jasonsbeer/Amiga-N2630/DataSheet/TimingDiagrams/6800-6502 STATE MACHINE READ.png

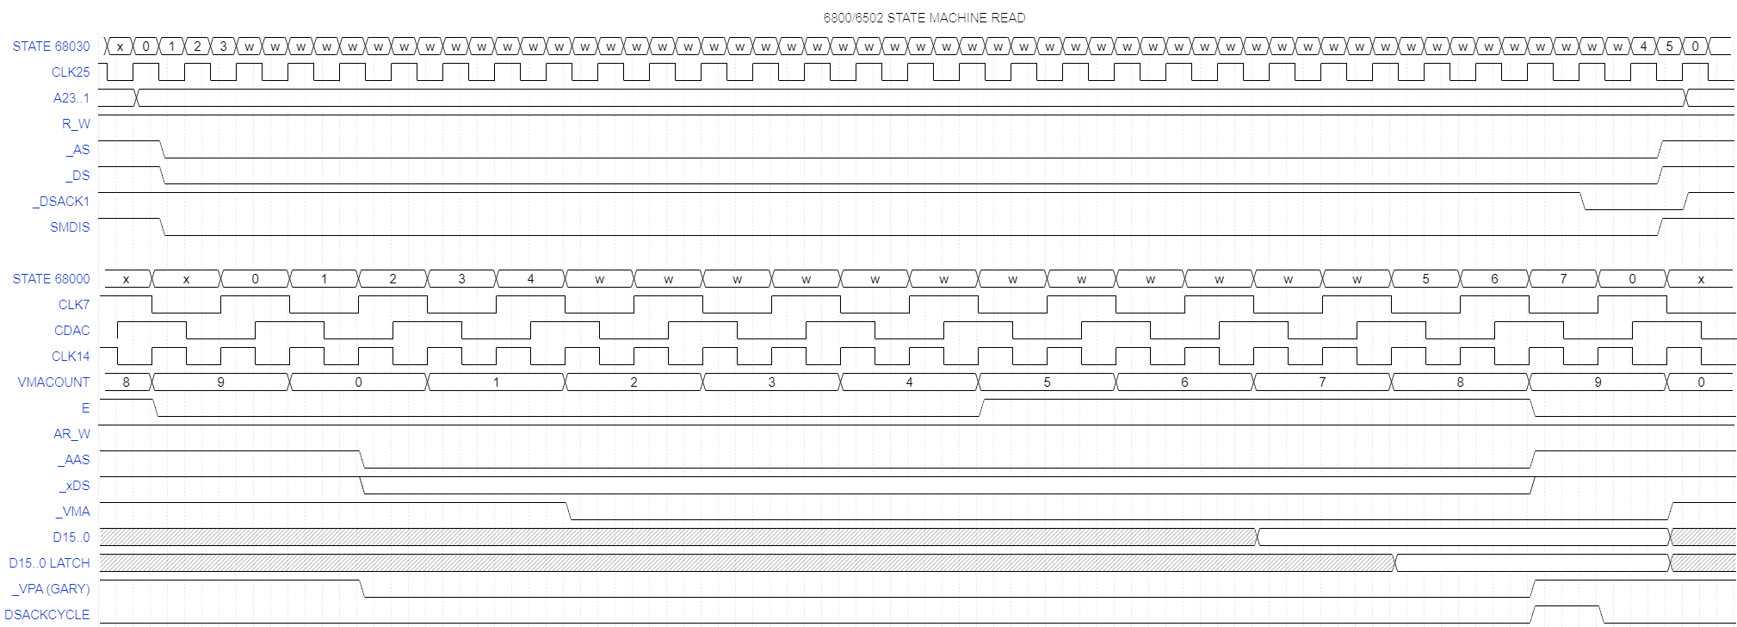
DataSheet/TimingDiagrams/6800-6502 STATE MACHINE READ.png
