jasonsbeer/Amiga-N2630/DataSheet/TimingDiagrams/68000 STATE MACHINE READ.png

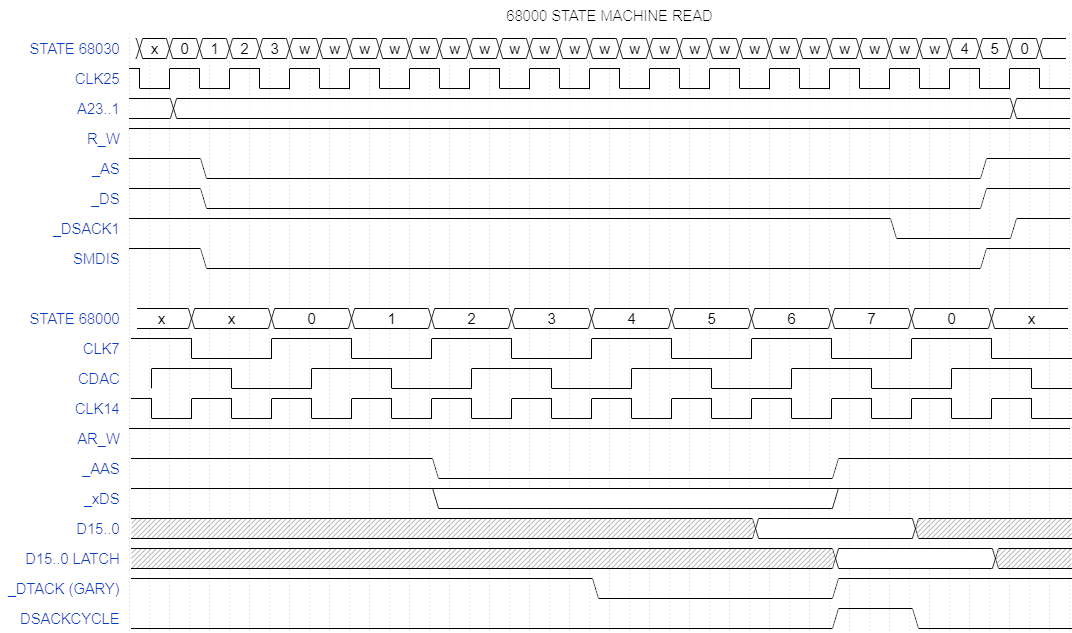
DataSheet/TimingDiagrams/68000 STATE MACHINE READ.png
