jasonsbeer/Amiga-N2630/DataSheet/TimingDiagrams/68000 STATE MACHINE WRITE.png

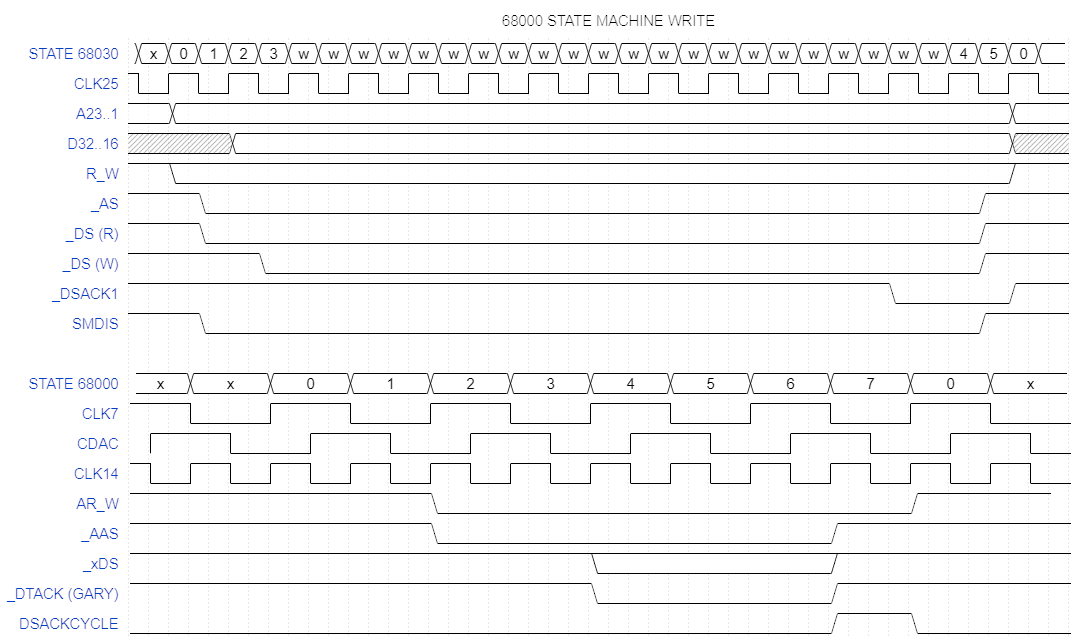
DataSheet/TimingDiagrams/68000 STATE MACHINE WRITE.png
