jasonsbeer/Amiga-N2630/DataSheet/TimingDiagrams/DMA STATE MACHINE READ.png

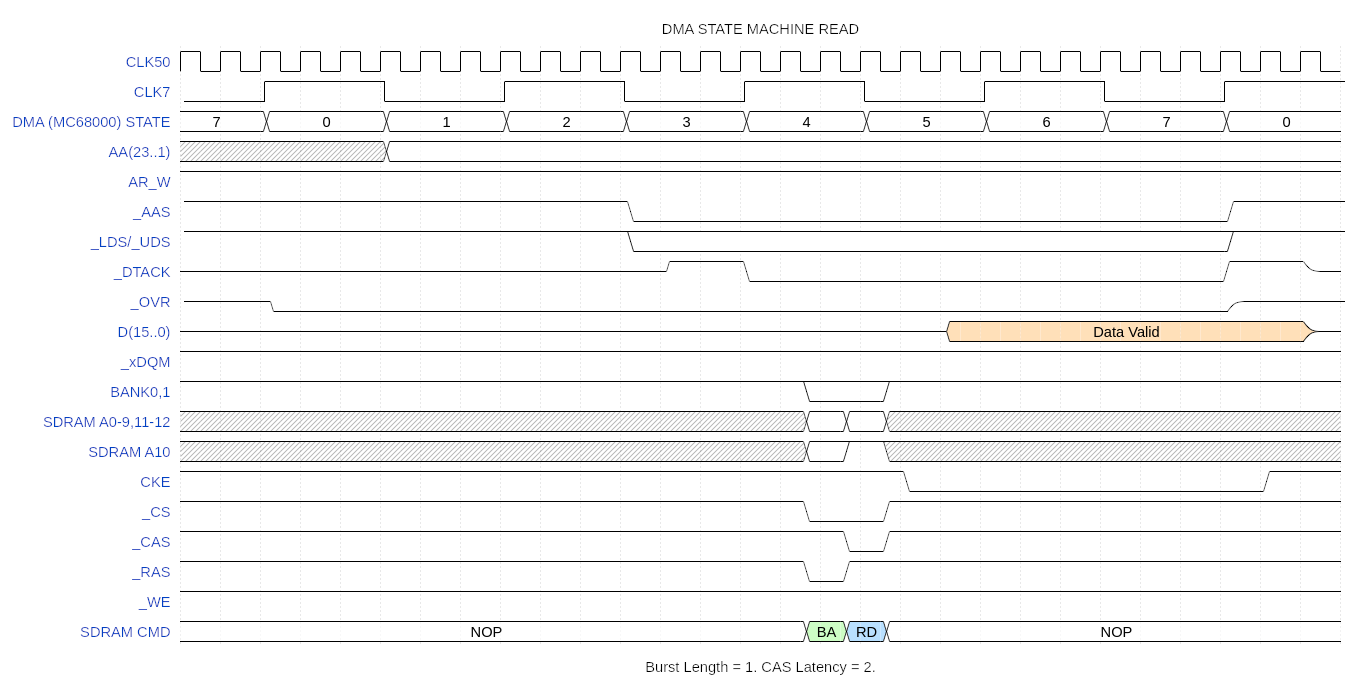
DataSheet/TimingDiagrams/DMA STATE MACHINE READ.png
