jasonsbeer/Amiga-N2630/DataSheet/TimingDiagrams/DMA STATE MACHINE WRITE.png

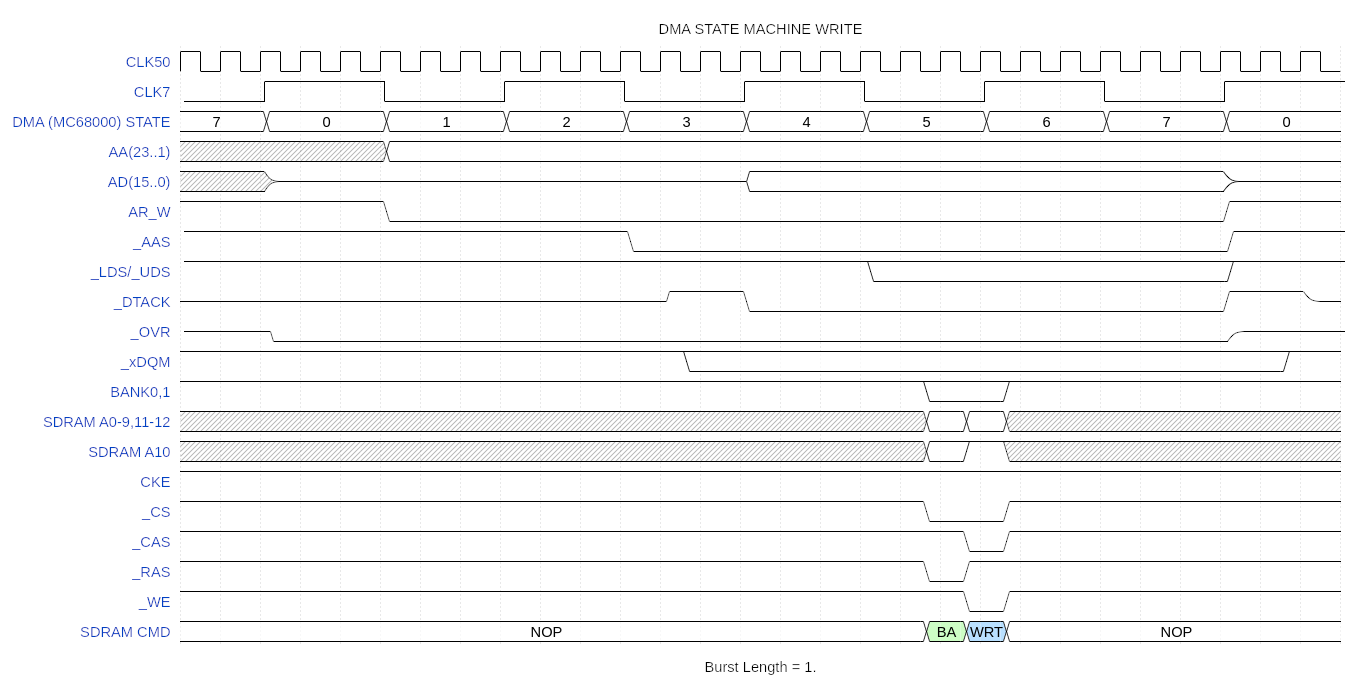
DataSheet/TimingDiagrams/DMA STATE MACHINE WRITE.png
