jasonsbeer/Amiga-N2630/DataSheet/TimingDiagrams/ZORRO2-SDRAM.png

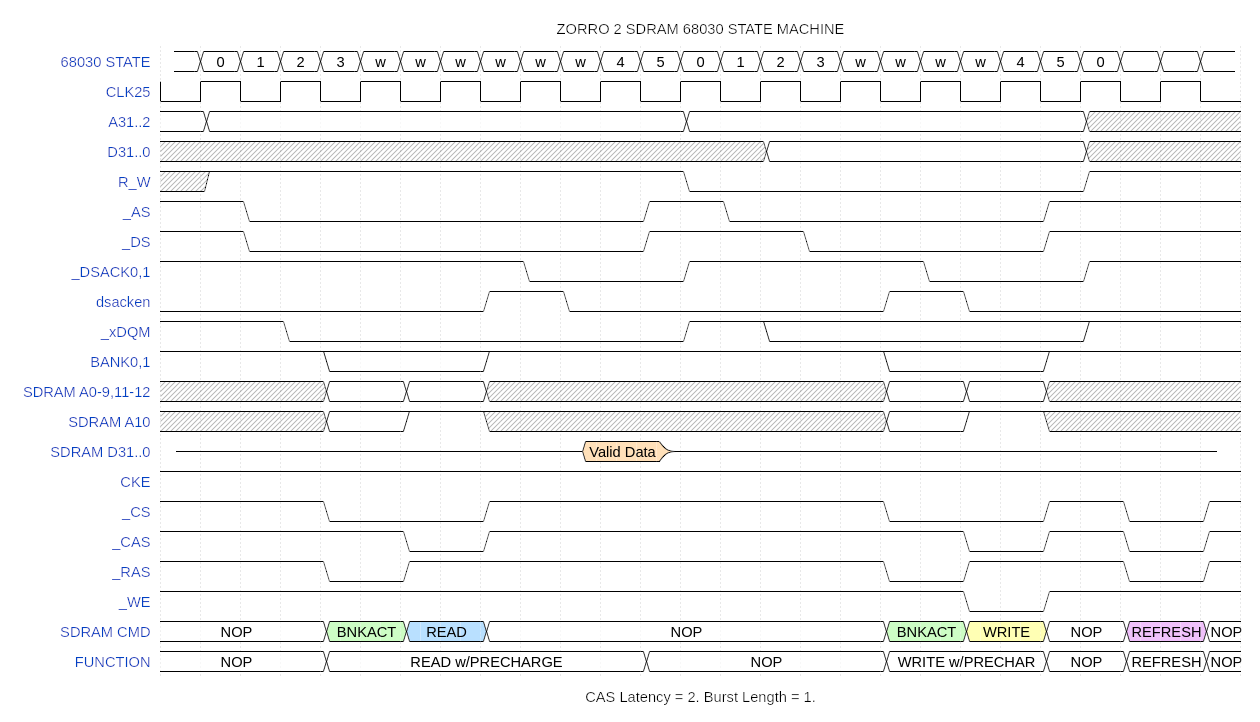
DataSheet/TimingDiagrams/ZORRO2-SDRAM.png
