jasonsbeer/Amiga-N2630/DataSheet/TimingDiagrams/ZORRO3-SDRAM.png

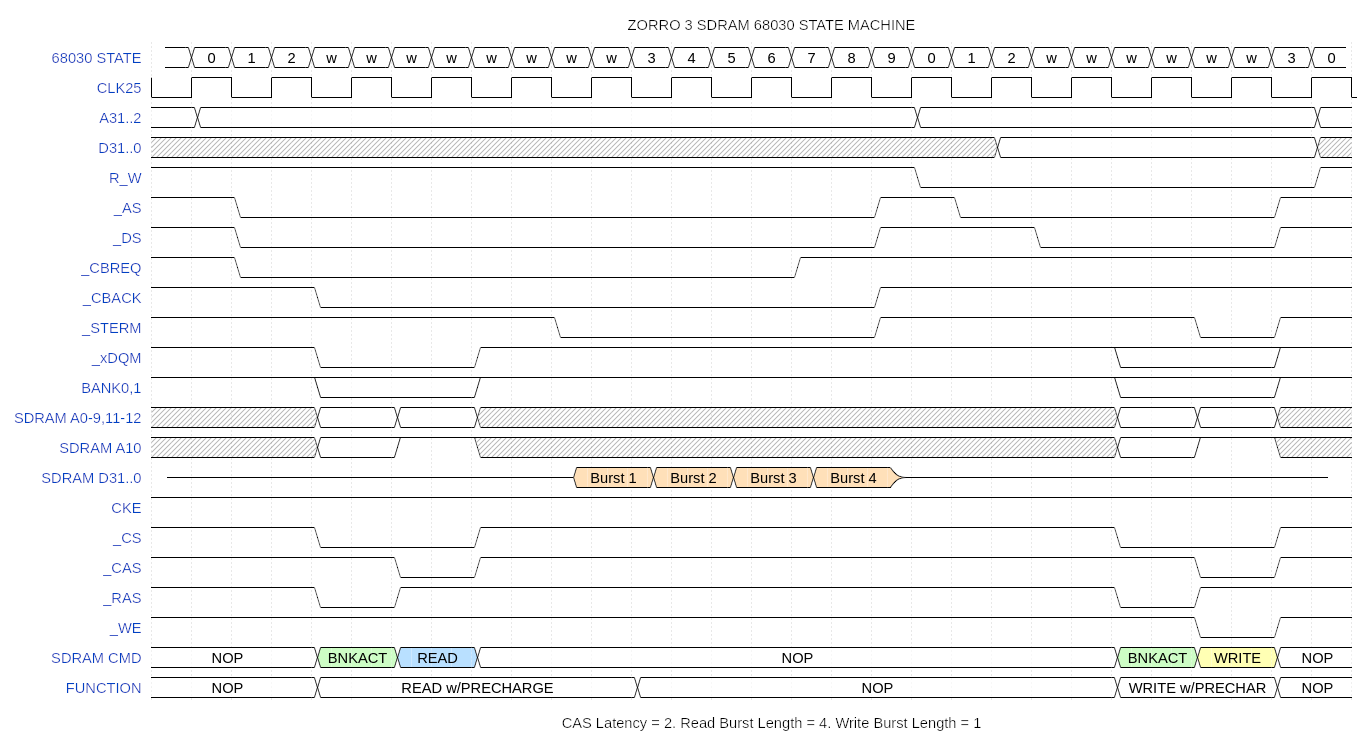
DataSheet/TimingDiagrams/ZORRO3-SDRAM.png
