jasonsbeer/Amiga-N2630/Images/N2630-30-small.jpg

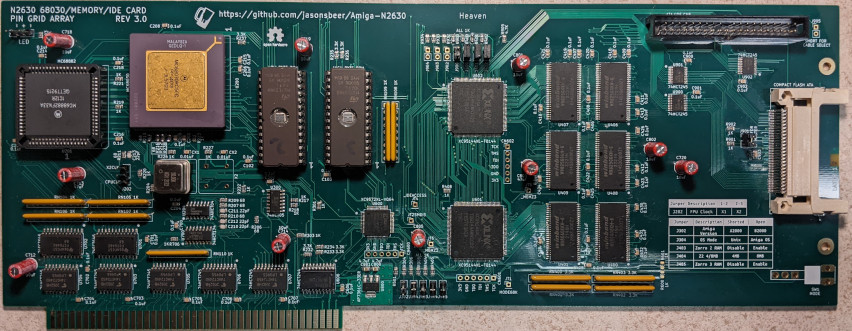
Images/N2630-30-small.jpg
