jasonsbeer/Amiga-N2630/Images/N2630-30D.png

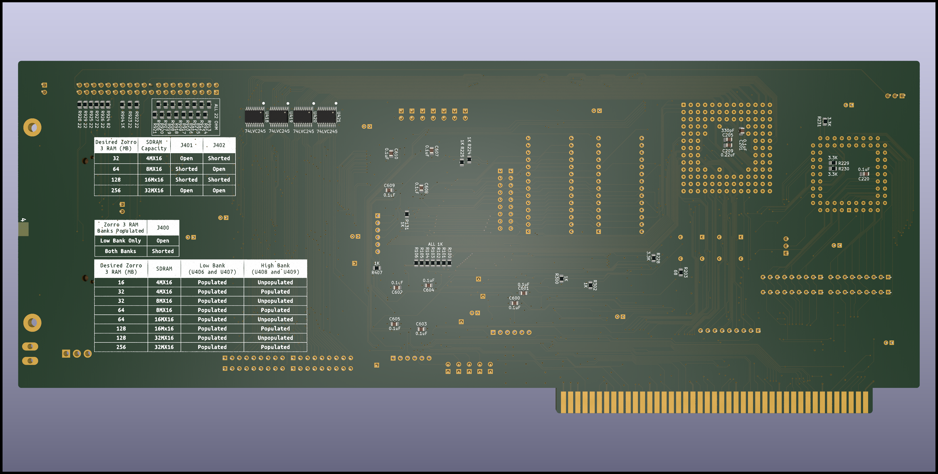
Images/N2630-30D.png
