jasonsbeer/Amiga-N2630/KiCAD/A2630-New-KiCAD-Rev410-PGA/BaseMemory.kicad_sch

## KiCad design KiCAD/A2630-New-KiCAD-Rev410-PGA/BaseMemory.kicad_sch (2024-03-27)

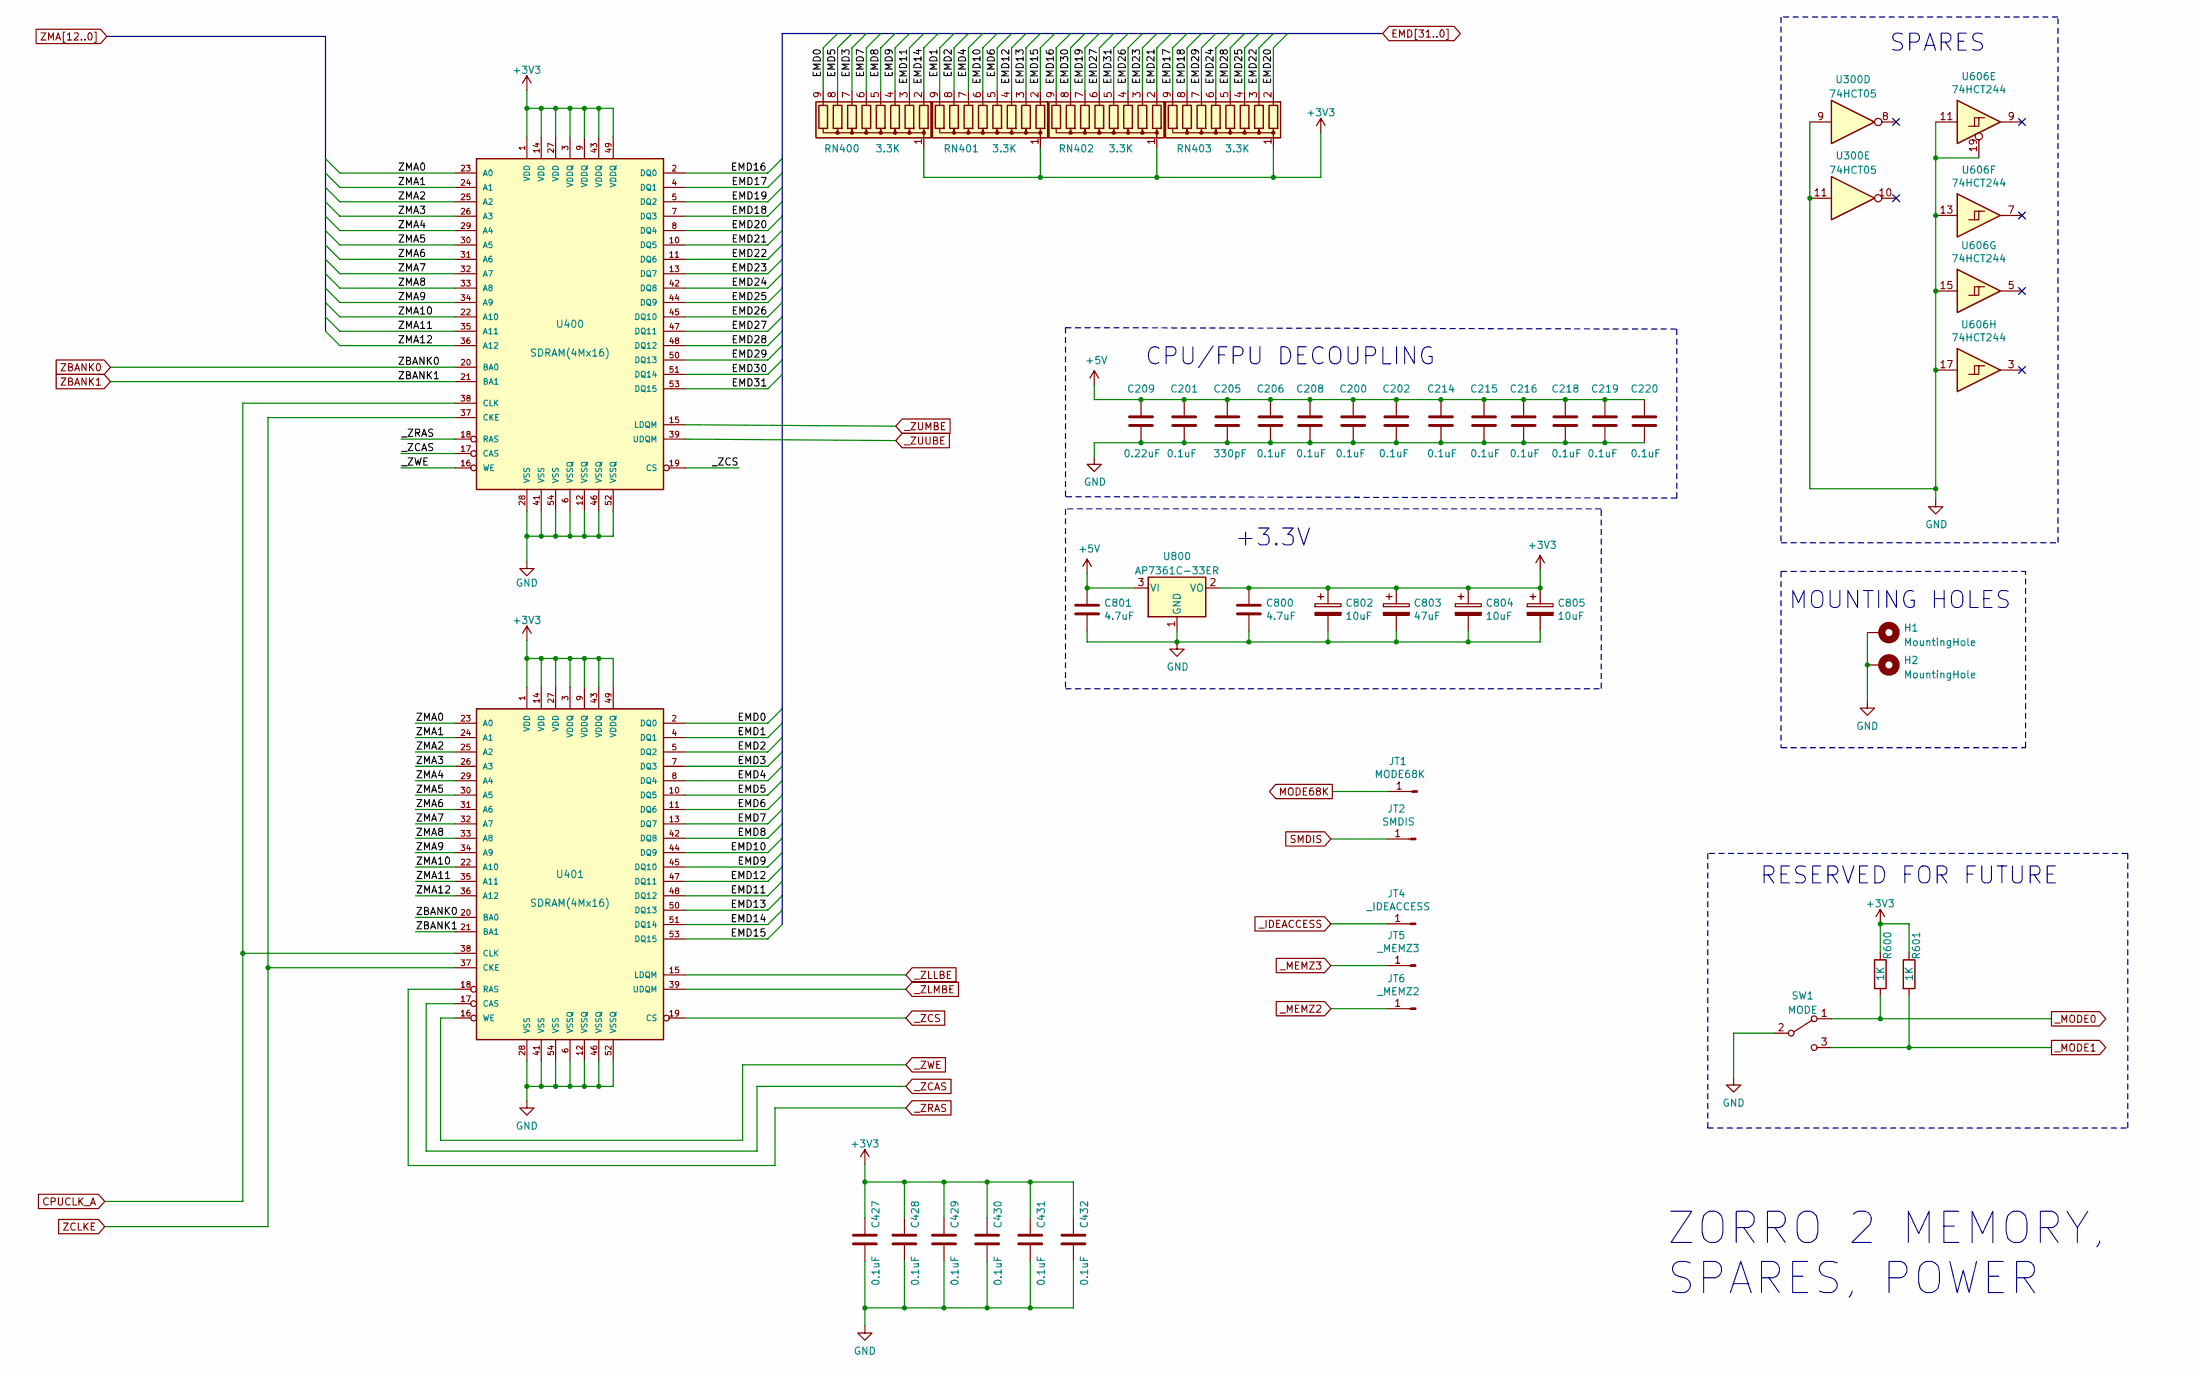
[picture p69: schematic BaseMemory.kicad_sch]

Parts:
C200, C201, C202, C206, C208, C214, C215, C216, C218, C219, C220, C427, C428, C429, C430, C431, C432: 0.1uF; C_0805_2012Metric
C205: 330pF; C_0805_2012Metric
C209: 0.22uF; C_0805_2012Metric
C800, C801: 4.7uF; C_0805_2012Metric
C802, C804, C805: 10uF; CP_Radial_D5.0mm_P2.00mm
C803: 47uF; CP_Radial_D5.0mm_P2.00mm
H1, H2: MountingHole; MountingHole_3.2mm_M3_Pad
JT1: MODE68K; PinHeader_1x01_P2.54mm_Vertical
JT2: SMDIS; PinHeader_1x01_P2.54mm_Vertical
JT4: _IDEACCESS; PinHeader_1x01_P2.54mm_Vertical
JT5: _MEMZ3; PinHeader_1x01_P2.54mm_Vertical
JT6: _MEMZ2; PinHeader_1x01_P2.54mm_Vertical
R600, R601: 1K; R_0805_2012Metric
RN400, RN401, RN402, RN403: 3.3K; R_Array_SIP9
SW1: MODE; 100SP1T1B1M7QE; PART 100SP1T1B1M7QE
U300: 74HCT05; SOIC-14_3.9x8.7mm_P1.27mm
U400, U401: SDRAM(4Mx16); TSOP-II-54_22.2x10.16mm_P0.8mm
U606: 74HCT244; SOIC-20W_7.5x12.8mm_P1.27mm
U800: AP7361C-33ER; SOT-223-3_TabPin2

Connections:
+3V3: C427.1, C428.1, C429.1, C430.1, C431.1, C432.1, C800.1, C802.1, C803.1, C804.1, C805.1, R600.1, R601.1, RN400.1 (common), RN401.1 (common), RN402.1 (common), RN403.1 (common), U400.1 (VDD), U400.3 (VDDQ), U400.9 (VDDQ), U400.14 (VDD), U400.27 (VDD), U400.43 (VDDQ), U400.49 (VDDQ), U401.1 (VDD), U401.3 (VDDQ), U401.9 (VDDQ), U401.14 (VDD), U401.27 (VDD), U401.43 (VDDQ), U401.49 (VDDQ), U800.2 (VO)
+5V: C200.1, C201.1, C202.1, C205.1, C206.1, C208.1, C209.1, C214.1, C215.1, C216.1, C218.1, C219.1, C220.1, C801.1, U800.3 (VI)
CPUCLK_A: U400.38 (CLK), U401.38 (CLK)
EMD0: RN400.9 (R8), U401.2 (DQ0)
EMD1: RN401.9 (R8), U401.4 (DQ1)
EMD2: RN401.8 (R7), U401.5 (DQ2)
EMD3: RN400.7 (R6), U401.7 (DQ3)
EMD4: RN401.7 (R6), U401.8 (DQ4)
EMD5: RN400.8 (R7), U401.10 (DQ5)
EMD6: RN401.5 (R4), U401.11 (DQ6)
EMD7: RN400.6 (R5), U401.13 (DQ7)
EMD8: RN400.5 (R4), U401.42 (DQ8)
EMD9: RN400.4 (R3), U401.45 (DQ10)
EMD10: RN401.6 (R5), U401.44 (DQ9)
EMD11: RN400.3 (R2), U401.48 (DQ12)
EMD12: RN401.4 (R3), U401.47 (DQ11)
EMD13: RN401.3 (R2), U401.50 (DQ13)
EMD14: RN400.2 (R1), U401.51 (DQ14)
EMD15: RN401.2 (R1), U401.53 (DQ15)
EMD16: RN402.9 (R8), U400.2 (DQ0)
EMD17: RN403.9 (R8), U400.4 (DQ1)
EMD18: RN403.8 (R7), U400.7 (DQ3)
EMD19: RN402.7 (R6), U400.5 (DQ2)
EMD20: RN403.2 (R1), U400.8 (DQ4)
EMD21: RN402.2 (R1), U400.10 (DQ5)
EMD22: RN403.3 (R2), U400.11 (DQ6)
EMD23: RN402.3 (R2), U400.13 (DQ7)
EMD24: RN403.6 (R5), U400.42 (DQ8)
EMD25: RN403.4 (R3), U400.44 (DQ9)
EMD26: RN402.4 (R3), U400.45 (DQ10)
EMD27: RN402.6 (R5), U400.47 (DQ11)
EMD28: RN403.5 (R4), U400.48 (DQ12)
EMD29: RN403.7 (R6), U400.50 (DQ13)
EMD30: RN402.8 (R7), U400.51 (DQ14)
EMD31: RN402.5 (R4), U400.53 (DQ15)
GND: C200.2, C201.2, C202.2, C205.2, C206.2, C208.2, C209.2, C214.2, C215.2, C216.2, C218.2, C219.2, C220.2, C427.2, C428.2, C429.2, C430.2, C431.2, C432.2, C800.2, C801.2, C802.2, C803.2, C804.2, C805.2, H1.1, H2.1, SW1.2 (B), U300.9, U300.11, U400.6 (VSSQ), U400.12 (VSSQ), U400.28 (VSS), U400.41 (VSS), U400.46 (VSSQ), U400.52 (VSSQ), U400.54 (VSS), U401.6 (VSSQ), U401.12 (VSSQ), U401.28 (VSS), U401.41 (VSS), U401.46 (VSSQ), U401.52 (VSSQ), U401.54 (VSS), U606.11, U606.13, U606.15, U606.17, U606.19, U800.1 (GND)
MODE68K: JT1.1
SMDIS: JT2.1
ZBANK0: U400.20 (BA0), U401.20 (BA0)
ZBANK1: U400.21 (BA1), U401.21 (BA1)
ZCLKE: U400.37 (CKE), U401.37 (CKE)
ZMA0: U400.23 (A0), U401.23 (A0)
ZMA1: U400.24 (A1), U401.24 (A1)
ZMA2: U400.25 (A2), U401.25 (A2)
ZMA3: U400.26 (A3), U401.26 (A3)
ZMA4: U400.29 (A4), U401.29 (A4)
ZMA5: U400.30 (A5), U401.30 (A5)
ZMA6: U400.31 (A6), U401.31 (A6)
ZMA7: U400.32 (A7), U401.32 (A7)
ZMA8: U400.33 (A8), U401.33 (A8)
ZMA9: U400.34 (A9), U401.34 (A9)
ZMA10: U400.22 (A10), U401.22 (A10)
ZMA11: U400.35 (A11), U401.35 (A11)
ZMA12: U400.36 (A12), U401.36 (A12)
_IDEACCESS: JT4.1
_MEMZ2: JT6.1
_MEMZ3: JT5.1
_MODE0: R600.2, SW1.1 (A)
_MODE1: R601.2, SW1.3 (C)
_ZCAS: U400.17 (CAS), U401.17 (CAS)
_ZCS: U400.19 (CS), U401.19 (CS)
_ZLLBE: U401.15 (LDQM)
_ZLMBE: U401.39 (UDQM)
_ZRAS: U400.18 (RAS), U401.18 (RAS)
_ZUMBE: U400.15 (LDQM)
_ZUUBE: U400.39 (UDQM)
_ZWE: U400.16 (WE), U401.16 (WE)

Notes on the sheet:
ZORRO 2 MEMORY, SPARES, POWER
MOUNTING HOLES
+3.3V
RESERVED FOR FUTURE
CPU/FPU DECOUPLING
SPARES
