jasonsbeer/Amiga-N2630/KiCAD/A2630-New-KiCAD-Rev410-PGA/CPLD1.kicad_sch

## KiCad design KiCAD/A2630-New-KiCAD-Rev410-PGA/CPLD1.kicad_sch (2024-03-27)

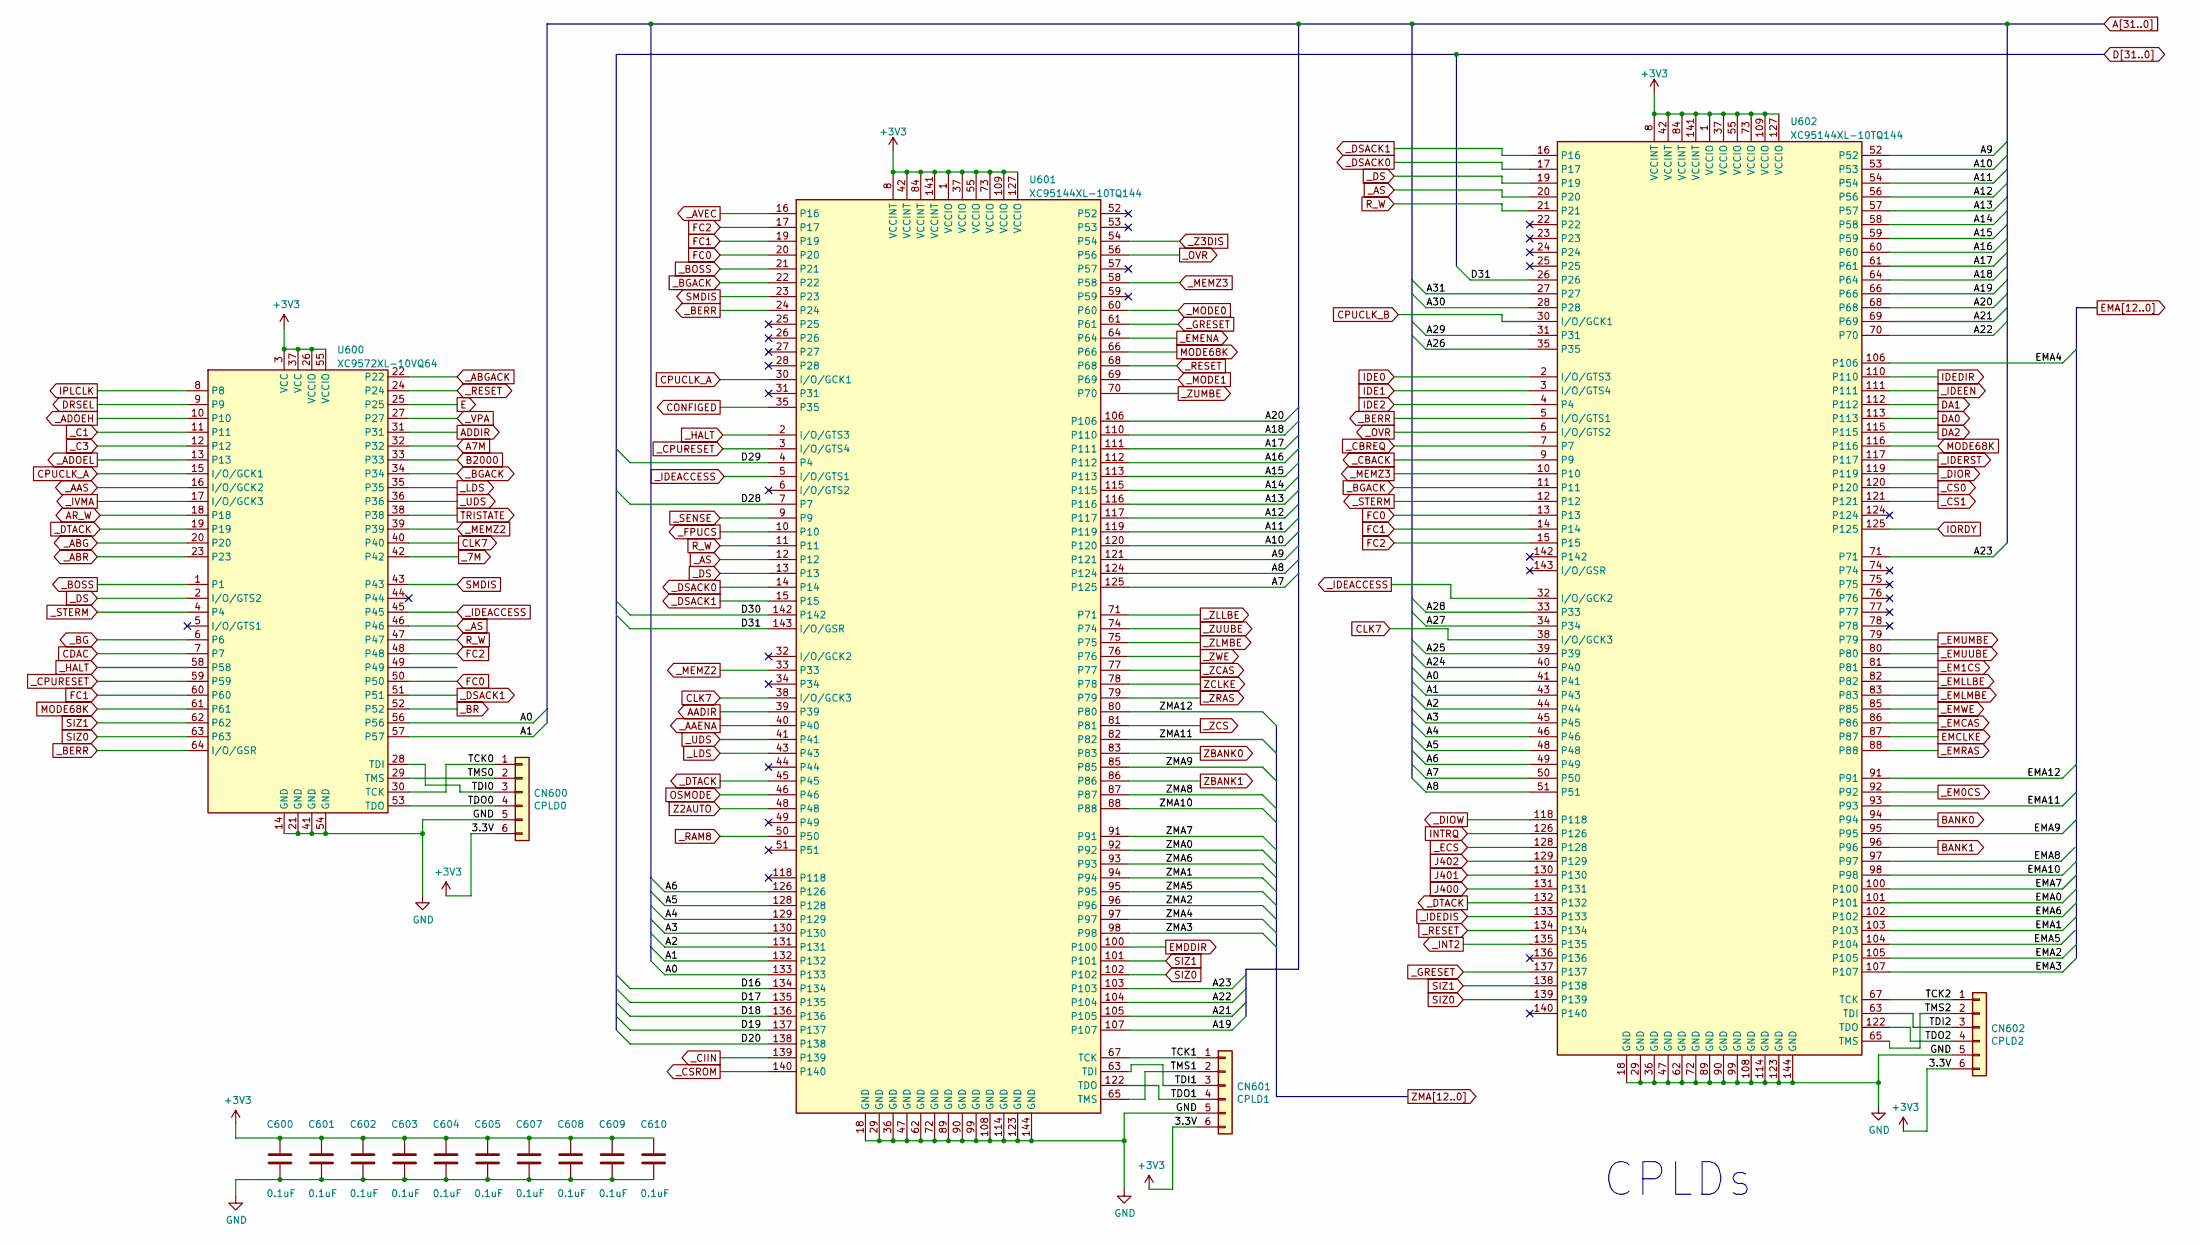
[picture p70: schematic CPLD1.kicad_sch]

Parts:
C600, C601, C602, C603, C604, C605, C607, C608, C609, C610: 0.1uF; C_0805_2012Metric
CN600: CPLD0; PinHeader_1x06_P2.54mm_Vertical
CN601: CPLD1; PinHeader_1x06_P2.54mm_Vertical
CN602: CPLD2; PinHeader_1x06_P2.54mm_Vertical
U600: XC9572XL-10VQ64; TQFP-64_10x10mm_P0.5mm
U601, U602: XC95144XL-10TQ144; TQFP-144_20x20mm_P0.5mm

Connections:
+3V3: C600.1, C601.1, C602.1, C603.1, C604.1, C605.1, C607.1, C608.1, C609.1, C610.1, CN600.6, CN601.6, CN602.6, U600.3 (VCC), U600.26 (VCCIO), U600.37 (VCC), U600.55 (VCCIO), U601.1 (VCCIO), U601.8 (VCCINT), U601.37 (VCCIO), U601.42 (VCCINT), U601.55 (VCCIO), U601.73 (VCCIO), U601.84 (VCCINT), U601.109 (VCCIO), U601.127 (VCCIO), U601.141 (VCCINT), U602.1 (VCCIO), U602.8 (VCCINT), U602.37 (VCCIO), U602.42 (VCCINT), U602.55 (VCCIO), U602.73 (VCCIO), U602.84 (VCCINT), U602.109 (VCCIO), U602.127 (VCCIO), U602.141 (VCCINT)
A0: U600.56, U601.133, U602.41
A1: U600.57, U601.132, U602.43
A2: U601.131, U602.44
A3: U601.130, U602.45
A4: U601.129, U602.46
A5: U601.128, U602.48
A6: U601.126, U602.49
A7: U601.125, U602.50
A7M: U600.32
A8: U601.124, U602.51
A9: U601.121, U602.52
A10: U601.120, U602.53
A11: U601.119, U602.54
A12: U601.117, U602.56
A13: U601.116, U602.57
A14: U601.115, U602.58
A15: U601.113, U602.59
A16: U601.112, U602.60
A17: U601.111, U602.61
A18: U601.110, U602.64
A19: U601.107, U602.66
A20: U601.106, U602.68
A21: U601.105, U602.69
A22: U601.104, U602.70
A23: U601.103, U602.71
A24: U602.40
A25: U602.39
A26: U602.35
A27: U602.34
A28: U602.33
A29: U602.31
A30: U602.28
A31: U602.27
AADIR: U601.39
ADDIR: U600.31
AR_W: U600.18
B2000: U600.33
BANK0: U602.94
BANK1: U602.96
CDAC: U600.7
CLK7: U600.40, U601.38 (I/O/GCK3), U602.38 (I/O/GCK3)
CONFIGED: U601.35
CPUCLK_A: U600.15 (I/O/GCK1), U601.30 (I/O/GCK1)
CPUCLK_B: U602.30 (I/O/GCK1)
D16: U601.134
D17: U601.135
D18: U601.136
D19: U601.137
D20: U601.138
D28: U601.7
D29: U601.4
D30: U601.142
D31: U601.143 (I/O/GSR), U602.26
DA0: U602.113
DA1: U602.112
DA2: U602.115
DRSEL: U600.9
E: U600.25
EMA0: U602.101
EMA1: U602.103
EMA2: U602.105
EMA3: U602.107
EMA4: U602.106
EMA5: U602.104
EMA6: U602.102
EMA7: U602.100
EMA8: U602.97
EMA9: U602.95
EMA10: U602.98
EMA11: U602.93
EMA12: U602.91
EMCLKE: U602.87
EMDDIR: U601.100
FC0: U600.50, U601.20, U602.13
FC1: U600.60, U601.19, U602.14
FC2: U600.48, U601.17, U602.15
GND: C600.2, C601.2, C602.2, C603.2, C604.2, C605.2, C607.2, C608.2, C609.2, C610.2, CN600.5, CN601.5, CN602.5, U600.14 (GND), U600.21 (GND), U600.41 (GND), U600.54 (GND), U601.18 (GND), U601.29 (GND), U601.36 (GND), U601.47 (GND), U601.62 (GND), U601.72 (GND), U601.89 (GND), U601.90 (GND), U601.99 (GND), U601.108 (GND), U601.114 (GND), U601.123 (GND), U601.144 (GND), U602.18 (GND), U602.29 (GND), U602.36 (GND), U602.47 (GND), U602.62 (GND), U602.72 (GND), U602.89 (GND), U602.90 (GND), U602.99 (GND), U602.108 (GND), U602.114 (GND), U602.123 (GND), U602.144 (GND)
IDE0: U602.2 (I/O/GTS3)
IDE1: U602.3 (I/O/GTS4)
IDE2: U602.4
IDEDIR: U602.110
INTRQ: U602.126
IORDY: U602.125
IPLCLK: U600.8
J400: U602.131
J401: U602.130
J402: U602.129
MODE68K: U600.61, U601.66, U602.116
OSMODE: U601.46
R_W: U600.47, U601.11, U602.21
SIZ0: U600.63, U601.102, U602.139
SIZ1: U600.62, U601.101, U602.138
SMDIS: U600.43, U601.23
TCK0: CN600.1, U600.30 (TCK)
TCK1: CN601.1, U601.67 (TCK)
TCK2: CN602.1, U602.67 (TCK)
TDI0: CN600.3, U600.28 (TDI)
TDI1: CN601.3, U601.63 (TDI)
TDI2: CN602.3, U602.63 (TDI)
TDO0: CN600.4, U600.53 (TDO)
TDO1: CN601.4, U601.122 (TDO)
TDO2: CN602.4, U602.122 (TDO)
TMS0: CN600.2, U600.29 (TMS)
TMS1: CN601.2, U601.65 (TMS)
TMS2: CN602.2, U602.65 (TMS)
TRISTATE: U600.38
Z2AUTO: U601.48
ZBANK0: U601.83
ZBANK1: U601.86
ZCLKE: U601.78
ZMA0: U601.92
ZMA1: U601.94
ZMA2: U601.96
ZMA3: U601.98
ZMA4: U601.97
ZMA5: U601.95
ZMA6: U601.93
ZMA7: U601.91
ZMA8: U601.87
ZMA9: U601.85
ZMA10: U601.88
ZMA11: U601.82
ZMA12: U601.80
_7M: U600.42
_AAENA: U601.40
_AAS: U600.16 (I/O/GCK2)
_ABG: U600.20
_ABGACK: U600.22
_ABR: U600.23
_ADOEH: U600.10
_ADOEL: U600.13
_AS: U600.46, U601.12, U602.20
_AVEC: U601.16
_BERR: U600.64 (I/O/GSR), U601.24, U602.5 (I/O/GTS1)
_BG: U600.6
_BGACK: U600.34, U601.22, U602.11
_BOSS: U600.1, U601.21
_BR: U600.52
_C1: U600.11
_C3: U600.12
_CBACK: U602.9
_CBREQ: U602.7
_CIIN: U601.139
_CPURESET: U600.59, U601.3 (I/O/GTS4)
_CS0: U602.120
_CS1: U602.121
_CSROM: U601.140
_DIOR: U602.119
_DIOW: U602.118
_DS: U600.2 (I/O/GTS2), U601.13, U602.19
_DSACK0: U601.14, U602.17
_DSACK1: U600.51, U601.15, U602.16
_DTACK: U600.19, U601.45, U602.132
_ECS: U602.128
_EM0CS: U602.92
_EM1CS: U602.81
_EMCAS: U602.86
_EMENA: U601.64
_EMLLBE: U602.82
_EMLMBE: U602.83
_EMRAS: U602.88
_EMUMBE: U602.79
_EMUUBE: U602.80
_EMWE: U602.85
_FPUCS: U601.10
_GRESET: U601.61, U602.137
_HALT: U600.58, U601.2 (I/O/GTS3)
_IDEACCESS: U600.45, U601.5 (I/O/GTS1), U602.32 (I/O/GCK2)
_IDEDIS: U602.133
_IDEEN: U602.111
_IDERST: U602.117
_INT2: U602.135
_IVMA: U600.17 (I/O/GCK3)
_LDS: U600.35, U601.43
_MEMZ2: U600.39, U601.33
_MEMZ3: U601.58, U602.10
_MODE0: U601.60
_MODE1: U601.69
_OVR: U601.56, U602.6 (I/O/GTS2)
_RAM8: U601.50
_RESET: U600.24, U601.68, U602.134
_SENSE: U601.9
_STERM: U600.4, U602.12
_UDS: U600.36, U601.41
_VPA: U600.27
_Z3DIS: U601.54
_ZCAS: U601.77
_ZCS: U601.81
_ZLLBE: U601.71
_ZLMBE: U601.75
_ZRAS: U601.79
_ZUMBE: U601.70
_ZUUBE: U601.74
_ZWE: U601.76

Notes on the sheet:
CPLDs
