jasonsbeer/Amiga-N2630/KiCAD/A2630-New-KiCAD-Rev410-PGA/Card Edge.kicad_sch

## KiCad design KiCAD/A2630-New-KiCAD-Rev410-PGA/Card Edge.kicad_sch (2024-03-27)

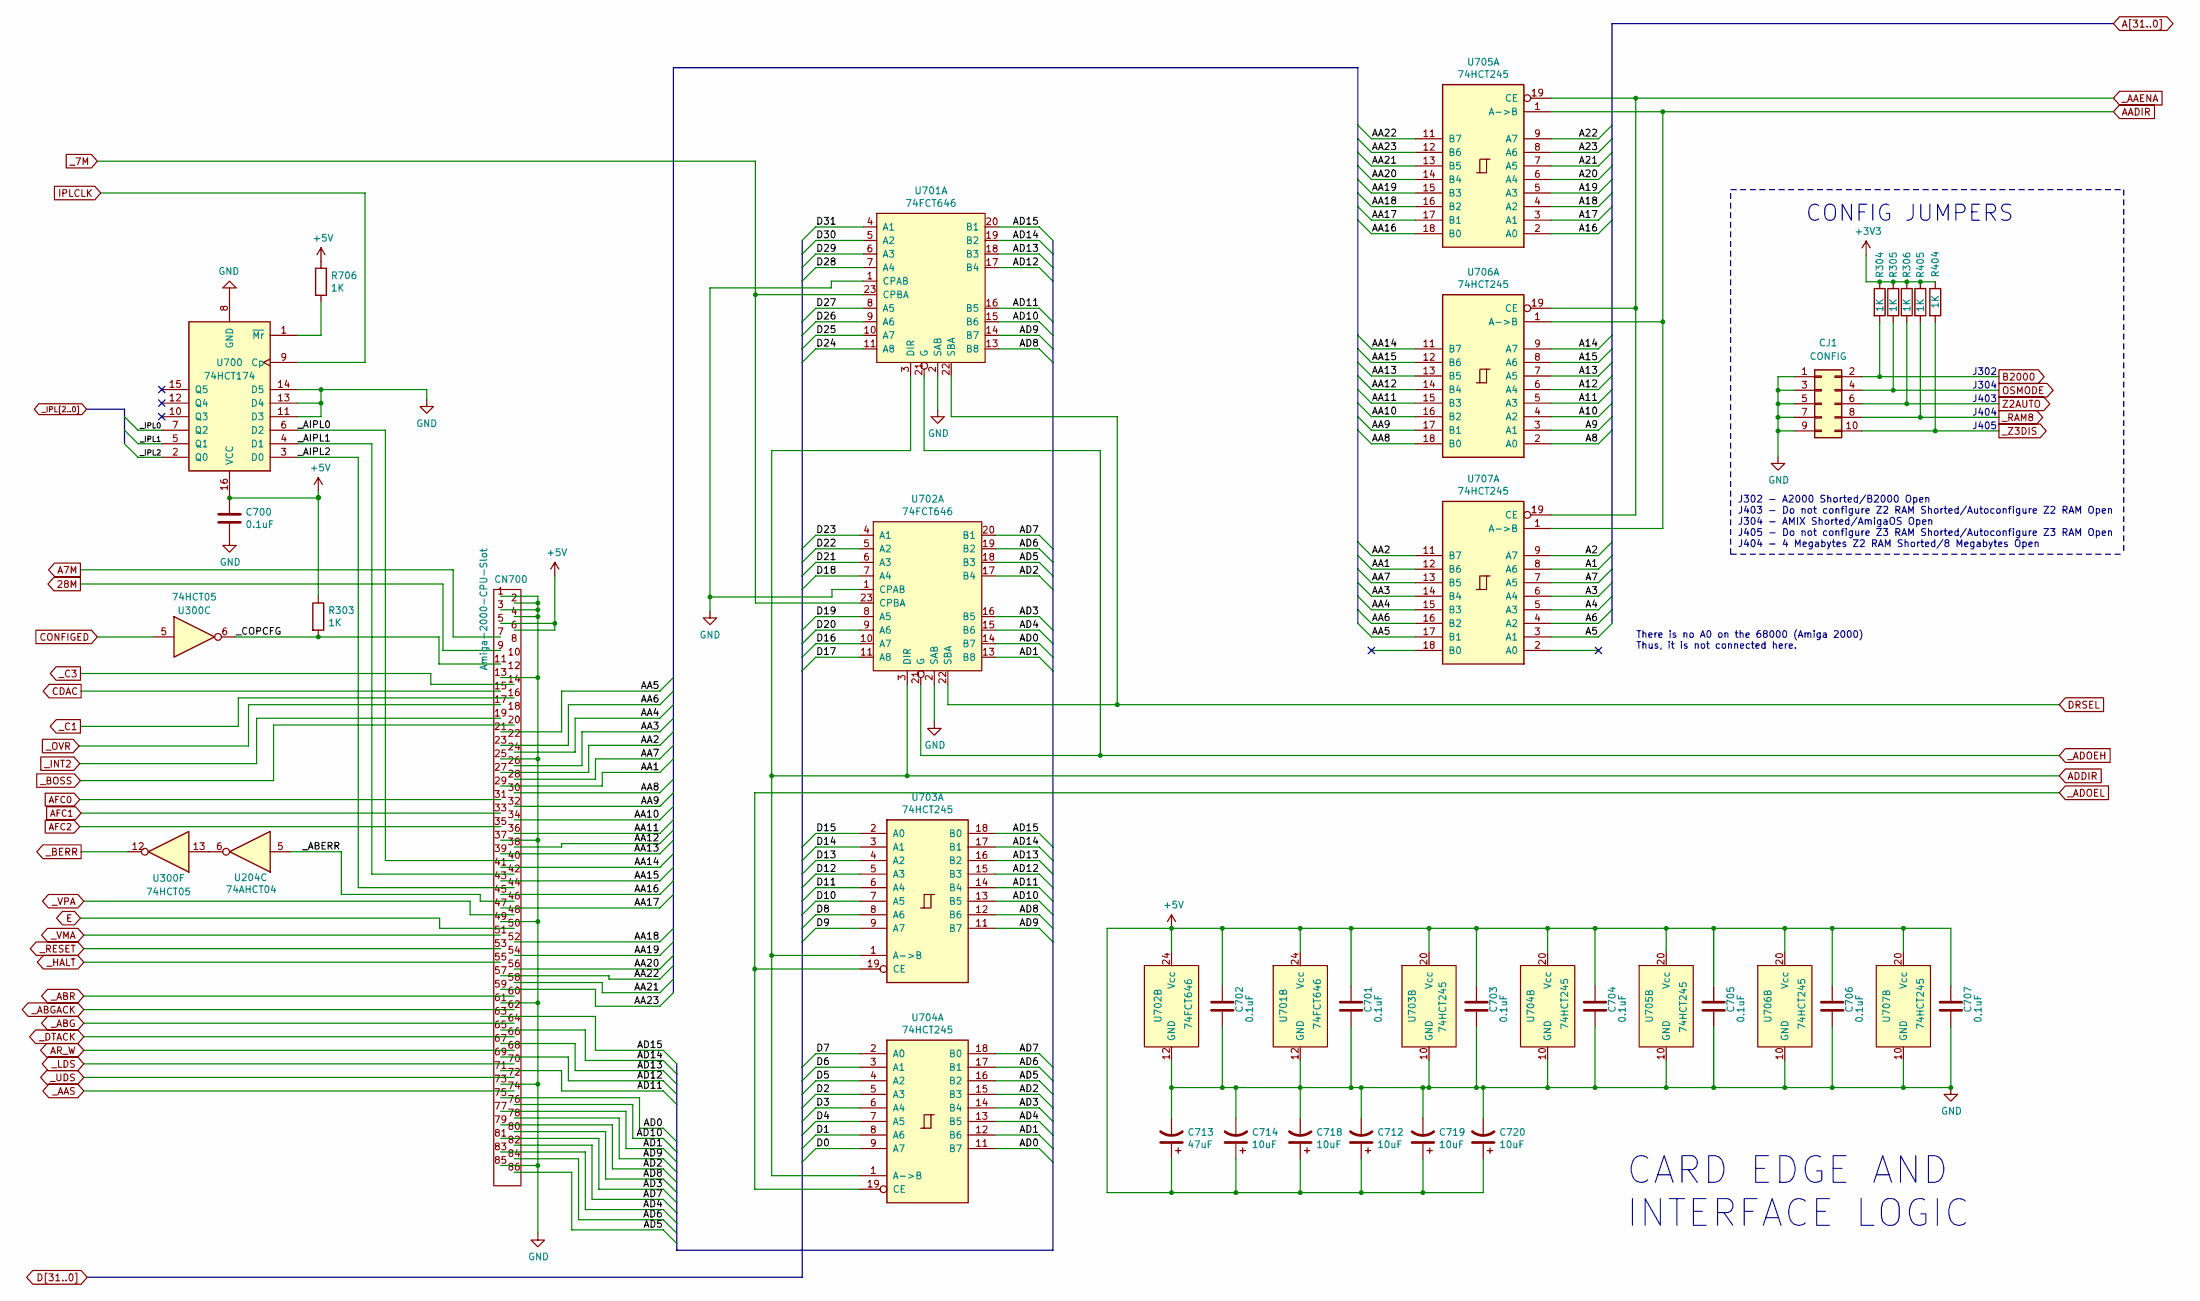
[picture p71: schematic Card Edge.kicad_sch]

Parts:
C700, C701, C702, C703, C704, C705, C706, C707: 0.1uF; C_0805_2012Metric
C712, C714, C718, C719, C720: 10uF; CP_Radial_D5.0mm_P2.00mm
C713: 47uF; CP_Radial_D5.0mm_P2.00mm
CJ1: CONFIG; PinHeader_2x05_P2.54mm_Vertical
CN700: Amiga-2000-CPU-Slot; A2000_CPUSLOT_MALE
R303, R304, R305, R306, R404, R405, R706: 1K; R_0805_2012Metric
U204: 74AHCT04; SOIC-14_3.9x8.7mm_P1.27mm; Digikey 296-31832-1-ND
U300: 74HCT05; SOIC-14_3.9x8.7mm_P1.27mm
U700: 74HCT174; SOIC-16_3.9x9.9mm_P1.27mm
U701, U702: 74FCT646; SOIC-24W_7.5x15.4mm_P1.27mm; Digikey 296-33244-5-ND
U703, U704, U705, U706, U707: 74HCT245; SOIC-20W_7.5x12.8mm_P1.27mm

Connections:
28M: CN700.9
+3V3: R304.1, R305.1, R306.1, R404.1, R405.1
+5V: C700.1, C701.1, C702.1, C703.1, C704.1, C705.1, C706.1, C707.1, C712.1, C713.1, C714.1, C718.1, C719.1, C720.1, CN700.5, CN700.6, R303.1, R706.1, U700.16 (VCC), U701.24 (Vcc), U702.24 (Vcc), U703.20 (Vcc), U704.20 (Vcc), U705.20 (Vcc), U706.20 (Vcc), U707.20 (Vcc)
A1: U707.8 (A6)
A2: U707.9 (A7)
A3: U707.6 (A4)
A4: U707.5 (A3)
A5: U707.3 (A1)
A6: U707.4 (A2)
A7: U707.7 (A5)
A7M: CN700.7
A8: U706.2 (A0)
A9: U706.3 (A1)
A10: U706.4 (A2)
A11: U706.5 (A3)
A12: U706.6 (A4)
A13: U706.7 (A5)
A14: U706.9 (A7)
A15: U706.8 (A6)
A16: U705.2 (A0)
A17: U705.3 (A1)
A18: U705.4 (A2)
A19: U705.5 (A3)
A20: U705.6 (A4)
A21: U705.7 (A5)
A22: U705.9 (A7)
A23: U705.8 (A6)
AA1: CN700.29, U707.12 (B6)
AA2: CN700.27, U707.11 (B7)
AA3: CN700.26, U707.14 (B4)
AA4: CN700.24, U707.15 (B3)
AA5: CN700.21, U707.17 (B1)
AA6: CN700.23, U707.16 (B2)
AA7: CN700.28, U707.13 (B5)
AA8: CN700.30, U706.18 (B0)
AA9: CN700.32, U706.17 (B1)
AA10: CN700.34, U706.16 (B2)
AA11: CN700.36, U706.15 (B3)
AA12: CN700.38, U706.14 (B4)
AA13: CN700.39, U706.13 (B5)
AA14: CN700.41, U706.11 (B7)
AA15: CN700.43, U706.12 (B6)
AA16: CN700.45, U705.18 (B0)
AA17: CN700.47, U705.17 (B1)
AA18: CN700.52, U705.16 (B2)
AA19: CN700.54, U705.15 (B3)
AA20: CN700.56, U705.14 (B4)
AA21: CN700.58, U705.13 (B5)
AA22: CN700.57, U705.11 (B7)
AA23: CN700.59, U705.12 (B6)
AADIR: U705.1 (A->B), U706.1 (A->B), U707.1 (A->B)
AD0: CN700.75, U702.14 (B7), U704.11 (B7)
AD1: CN700.77, U702.13 (B8), U704.12 (B6)
AD2: CN700.79, U702.17 (B4), U704.15 (B3)
AD3: CN700.81, U702.16 (B5), U704.14 (B4)
AD4: CN700.83, U702.15 (B6), U704.13 (B5)
AD5: CN700.86, U702.18 (B3), U704.16 (B2)
AD6: CN700.84, U702.19 (B2), U704.17 (B1)
AD7: CN700.82, U702.20 (B1), U704.18 (B0)
AD8: CN700.80, U701.13 (B8), U703.12 (B6)
AD9: CN700.78, U701.14 (B7), U703.11 (B7)
AD10: CN700.76, U701.15 (B6), U703.13 (B5)
AD11: CN700.71, U701.16 (B5), U703.14 (B4)
AD12: CN700.69, U701.17 (B4), U703.15 (B3)
AD13: CN700.67, U701.18 (B3), U703.16 (B2)
AD14: CN700.65, U701.19 (B2), U703.17 (B1)
AD15: CN700.63, U701.20 (B1), U703.18 (B0)
ADDIR: U701.3 (DIR), U702.3 (DIR), U703.1 (A->B), U704.1 (A->B)
AFC0: CN700.31
AFC1: CN700.33
AFC2: CN700.35
AR_W: CN700.68
B2000: CJ1.2, R304.2
CDAC: CN700.15
CONFIGED: U300.5
D0: U704.9 (A7)
D1: U704.8 (A6)
D2: U704.5 (A3)
D3: U704.6 (A4)
D4: U704.7 (A5)
D5: U704.4 (A2)
D6: U704.3 (A1)
D7: U704.2 (A0)
D8: U703.8 (A6)
D9: U703.9 (A7)
D10: U703.7 (A5)
D11: U703.6 (A4)
D12: U703.5 (A3)
D13: U703.4 (A2)
D14: U703.3 (A1)
D15: U703.2 (A0)
D16: U702.10 (A7)
D17: U702.11 (A8)
D18: U702.7 (A4)
D19: U702.8 (A5)
D20: U702.9 (A6)
D21: U702.6 (A3)
D22: U702.5 (A2)
D23: U702.4 (A1)
D24: U701.11 (A8)
D25: U701.10 (A7)
D26: U701.9 (A6)
D27: U701.8 (A5)
D28: U701.7 (A4)
D29: U701.6 (A3)
D30: U701.5 (A2)
D31: U701.4 (A1)
DRSEL: U701.22 (SBA), U702.22 (SBA)
E: CN700.50
GND: C700.2, C701.2, C702.2, C703.2, C704.2, C705.2, C706.2, C707.2, C712.2, C713.2, C714.2, C718.2, C719.2, C720.2, CJ1.1, CJ1.3, CJ1.5, CJ1.7, CJ1.9, CN700.1, CN700.2, CN700.3, CN700.4, CN700.13, CN700.25, CN700.37, CN700.49, CN700.61, CN700.73, CN700.85, U700.8 (GND), U700.11 (D3), U700.13 (D4), U700.14 (D5), U701.1 (CPAB), U701.2 (SAB), U701.12 (GND), U702.1 (CPAB), U702.2 (SAB), U702.12 (GND), U703.10 (GND), U704.10 (GND), U705.10 (GND), U706.10 (GND), U707.10 (GND)
IPLCLK: U700.9 (Cp)
unnamed: R706.2, U700.1 (~Mr)
unnamed: U204.6, U300.13
OSMODE: CJ1.4, R305.2
Z2AUTO: CJ1.6, R306.2
_7M: U701.23 (CPBA), U702.23 (CPBA)
_AAENA: U705.19 (CE), U706.19 (CE), U707.19 (CE)
_AAS: CN700.74
_ABERR: CN700.46, U204.5
_ABG: CN700.64
_ABGACK: CN700.62
_ABR: CN700.60
_ADOEH: U701.21 (G), U702.21 (G)
_ADOEL: U703.19 (CE), U704.19 (CE)
_AIPL0: CN700.40, U700.6 (D2)
_AIPL1: CN700.42, U700.4 (D1)
_AIPL2: CN700.44, U700.3 (D0)
_BERR: U300.12
_BOSS: CN700.20
_C1: CN700.16
_C3: CN700.14
_COPCFG: CN700.11, R303.2, U300.6
_DTACK: CN700.66
_HALT: CN700.55
_INT2: CN700.19
_IPL0: U700.7 (Q2)
_IPL1: U700.5 (Q1)
_IPL2: U700.2 (Q0)
_LDS: CN700.70
_OVR: CN700.17
_RAM8: CJ1.8, R405.2
_RESET: CN700.53
_UDS: CN700.72
_VMA: CN700.51
_VPA: CN700.48
_Z3DIS: CJ1.10, R404.2

Notes on the sheet:
CONFIG JUMPERS
J404
J302 - A2000 Shorted/B2000 Open J403 - Do not configure Z2 RAM Shorted/Autoconfigure Z2 RAM Open J304 - AMIX Shorted/AmigaOS Open J405 - Do not configure Z3 RAM Shorted/Autoconfigure Z3 RAM Open J404 - 4 Megabytes Z2 RAM Shorted/8 Megabytes Open
There is no A0 on the 68000 (Amiga 2000) Thus, it is not connected here.
J302
J304
J405
J403
CARD EDGE AND INTERFACE LOGIC
