jasonsbeer/Amiga-N2630/KiCAD/A2630-New-KiCAD-Rev410-PGA/ExpansionMemory.kicad_sch

## KiCad design KiCAD/A2630-New-KiCAD-Rev410-PGA/ExpansionMemory.kicad_sch (2024-03-27)

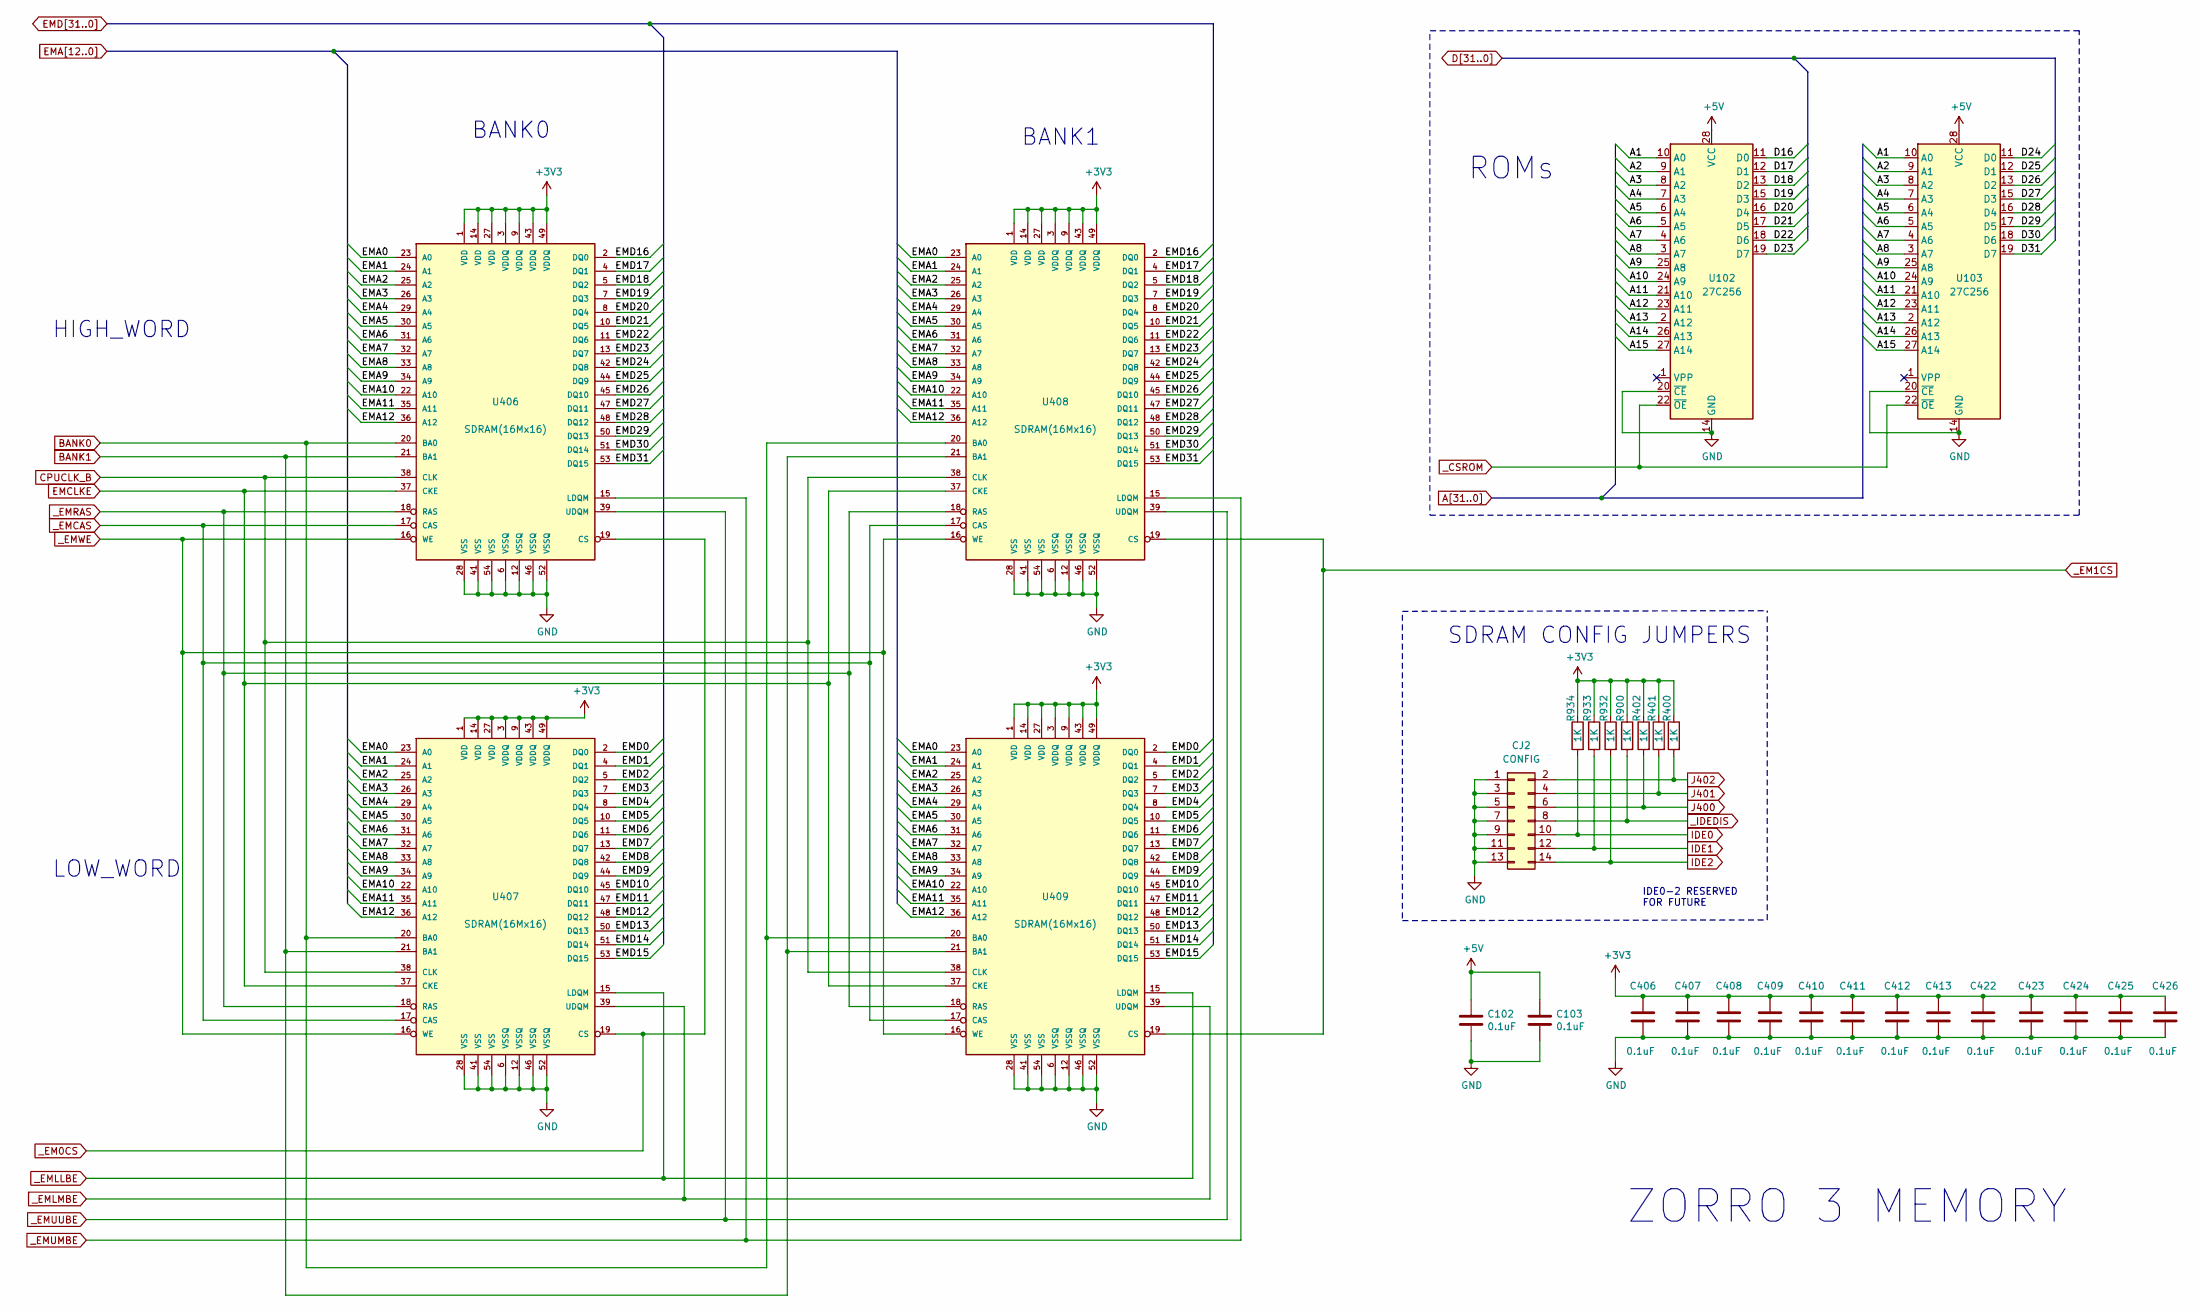
[picture p72: schematic ExpansionMemory.kicad_sch]

Parts:
C102, C103, C406, C407, C408, C409, C410, C411, C412, C413, C422, C423, C424, C425, C426: 0.1uF; C_0805_2012Metric
CJ2: CONFIG; PinHeader_2x07_P2.54mm_Vertical
R400, R401, R402, R900, R932, R933, R934: 1K; R_0805_2012Metric
U102, U103: 27C256; DIP-28_W15.24mm
U406, U407, U408, U409: SDRAM(16Mx16); TSOP-II-54_22.2x10.16mm_P0.8mm

Connections:
+3V3: C406.1, C407.1, C408.1, C409.1, C410.1, C411.1, C412.1, C413.1, C422.1, C423.1, C424.1, C425.1, C426.1, R400.1, R401.1, R402.1, R900.1, R932.1, R933.1, R934.1, U406.1 (VDD), U406.3 (VDDQ), U406.9 (VDDQ), U406.14 (VDD), U406.27 (VDD), U406.43 (VDDQ), U406.49 (VDDQ), U407.1 (VDD), U407.3 (VDDQ), U407.9 (VDDQ), U407.14 (VDD), U407.27 (VDD), U407.43 (VDDQ), U407.49 (VDDQ), U408.1 (VDD), U408.3 (VDDQ), U408.9 (VDDQ), U408.14 (VDD), U408.27 (VDD), U408.43 (VDDQ), U408.49 (VDDQ), U409.1 (VDD), U409.3 (VDDQ), U409.9 (VDDQ), U409.14 (VDD), U409.27 (VDD), U409.43 (VDDQ), U409.49 (VDDQ)
+5V: C102.1, C103.1, U102.28 (VCC), U103.28 (VCC)
A1: U102.10 (A0), U103.10 (A0)
A2: U102.9 (A1), U103.9 (A1)
A3: U102.8 (A2), U103.8 (A2)
A4: U102.7 (A3), U103.7 (A3)
A5: U102.6 (A4), U103.6 (A4)
A6: U102.5 (A5), U103.5 (A5)
A7: U102.4 (A6), U103.4 (A6)
A8: U102.3 (A7), U103.3 (A7)
A9: U102.25 (A8), U103.25 (A8)
A10: U102.24 (A9), U103.24 (A9)
A11: U102.21 (A10), U103.21 (A10)
A12: U102.23 (A11), U103.23 (A11)
A13: U102.2 (A12), U103.2 (A12)
A14: U102.26 (A13), U103.26 (A13)
A15: U102.27 (A14), U103.27 (A14)
BANK0: U406.20 (BA0), U407.20 (BA0), U408.20 (BA0), U409.20 (BA0)
BANK1: U406.21 (BA1), U407.21 (BA1), U408.21 (BA1), U409.21 (BA1)
CPUCLK_B: U406.38 (CLK), U407.38 (CLK), U408.38 (CLK), U409.38 (CLK)
D16: U102.11 (D0)
D17: U102.12 (D1)
D18: U102.13 (D2)
D19: U102.15 (D3)
D20: U102.16 (D4)
D21: U102.17 (D5)
D22: U102.18 (D6)
D23: U102.19 (D7)
D24: U103.11 (D0)
D25: U103.12 (D1)
D26: U103.13 (D2)
D27: U103.15 (D3)
D28: U103.16 (D4)
D29: U103.17 (D5)
D30: U103.18 (D6)
D31: U103.19 (D7)
EMA0: U406.23 (A0), U407.23 (A0), U408.23 (A0), U409.23 (A0)
EMA1: U406.24 (A1), U407.24 (A1), U408.24 (A1), U409.24 (A1)
EMA2: U406.25 (A2), U407.25 (A2), U408.25 (A2), U409.25 (A2)
EMA3: U406.26 (A3), U407.26 (A3), U408.26 (A3), U409.26 (A3)
EMA4: U406.29 (A4), U407.29 (A4), U408.29 (A4), U409.29 (A4)
EMA5: U406.30 (A5), U407.30 (A5), U408.30 (A5), U409.30 (A5)
EMA6: U406.31 (A6), U407.31 (A6), U408.31 (A6), U409.31 (A6)
EMA7: U406.32 (A7), U407.32 (A7), U408.32 (A7), U409.32 (A7)
EMA8: U406.33 (A8), U407.33 (A8), U408.33 (A8), U409.33 (A8)
EMA9: U406.34 (A9), U407.34 (A9), U408.34 (A9), U409.34 (A9)
EMA10: U406.22 (A10), U407.22 (A10), U408.22 (A10), U409.22 (A10)
EMA11: U406.35 (A11), U407.35 (A11), U408.35 (A11), U409.35 (A11)
EMA12: U406.36 (A12), U407.36 (A12), U408.36 (A12), U409.36 (A12)
EMCLKE: U406.37 (CKE), U407.37 (CKE), U408.37 (CKE), U409.37 (CKE)
EMD0: U407.2 (DQ0), U409.2 (DQ0)
EMD1: U407.4 (DQ1), U409.4 (DQ1)
EMD2: U407.5 (DQ2), U409.5 (DQ2)
EMD3: U407.7 (DQ3), U409.7 (DQ3)
EMD4: U407.8 (DQ4), U409.8 (DQ4)
EMD5: U407.10 (DQ5), U409.10 (DQ5)
EMD6: U407.11 (DQ6), U409.11 (DQ6)
EMD7: U407.13 (DQ7), U409.13 (DQ7)
EMD8: U407.42 (DQ8), U409.42 (DQ8)
EMD9: U407.44 (DQ9), U409.44 (DQ9)
EMD10: U407.45 (DQ10), U409.45 (DQ10)
EMD11: U407.47 (DQ11), U409.47 (DQ11)
EMD12: U407.48 (DQ12), U409.48 (DQ12)
EMD13: U407.50 (DQ13), U409.50 (DQ13)
EMD14: U407.51 (DQ14), U409.51 (DQ14)
EMD15: U407.53 (DQ15), U409.53 (DQ15)
EMD16: U406.2 (DQ0), U408.2 (DQ0)
EMD17: U406.4 (DQ1), U408.4 (DQ1)
EMD18: U406.5 (DQ2), U408.5 (DQ2)
EMD19: U406.7 (DQ3), U408.7 (DQ3)
EMD20: U406.8 (DQ4), U408.8 (DQ4)
EMD21: U406.10 (DQ5), U408.10 (DQ5)
EMD22: U406.11 (DQ6), U408.11 (DQ6)
EMD23: U406.13 (DQ7), U408.13 (DQ7)
EMD24: U406.42 (DQ8), U408.42 (DQ8)
EMD25: U406.44 (DQ9), U408.44 (DQ9)
EMD26: U406.45 (DQ10), U408.45 (DQ10)
EMD27: U406.47 (DQ11), U408.47 (DQ11)
EMD28: U406.48 (DQ12), U408.48 (DQ12)
EMD29: U406.50 (DQ13), U408.50 (DQ13)
EMD30: U406.51 (DQ14), U408.51 (DQ14)
EMD31: U406.53 (DQ15), U408.53 (DQ15)
GND: C102.2, C103.2, C406.2, C407.2, C408.2, C409.2, C410.2, C411.2, C412.2, C413.2, C422.2, C423.2, C424.2, C425.2, C426.2, CJ2.1, CJ2.3, CJ2.5, CJ2.7, CJ2.9, CJ2.11, CJ2.13, U102.14 (GND), U102.20 (~CE), U103.14 (GND), U103.20 (~CE), U406.6 (VSSQ), U406.12 (VSSQ), U406.28 (VSS), U406.41 (VSS), U406.46 (VSSQ), U406.52 (VSSQ), U406.54 (VSS), U407.6 (VSSQ), U407.12 (VSSQ), U407.28 (VSS), U407.41 (VSS), U407.46 (VSSQ), U407.52 (VSSQ), U407.54 (VSS), U408.6 (VSSQ), U408.12 (VSSQ), U408.28 (VSS), U408.41 (VSS), U408.46 (VSSQ), U408.52 (VSSQ), U408.54 (VSS), U409.6 (VSSQ), U409.12 (VSSQ), U409.28 (VSS), U409.41 (VSS), U409.46 (VSSQ), U409.52 (VSSQ), U409.54 (VSS)
IDE0: CJ2.10, R934.2
IDE1: CJ2.12, R933.2
IDE2: CJ2.14, R932.2
J400: CJ2.6, R402.2
J401: CJ2.4, R401.2
J402: CJ2.2, R400.2
_CSROM: U102.22 (~OE), U103.22 (~OE)
_EM0CS: U406.19 (CS), U407.19 (CS)
_EM1CS: U408.19 (CS), U409.19 (CS)
_EMCAS: U406.17 (CAS), U407.17 (CAS), U408.17 (CAS), U409.17 (CAS)
_EMLLBE: U407.15 (LDQM), U409.15 (LDQM)
_EMLMBE: U407.39 (UDQM), U409.39 (UDQM)
_EMRAS: U406.18 (RAS), U407.18 (RAS), U408.18 (RAS), U409.18 (RAS)
_EMUMBE: U406.15 (LDQM), U408.15 (LDQM)
_EMUUBE: U406.39 (UDQM), U408.39 (UDQM)
_EMWE: U406.16 (WE), U407.16 (WE), U408.16 (WE), U409.16 (WE)
_IDEDIS: CJ2.8, R900.2

Notes on the sheet:
ZORRO 3 MEMORY
IDE0-2 RESERVED FOR FUTURE
SDRAM CONFIG JUMPERS
HIGH_WORD
BANK1
BANK0
ROMs
LOW_WORD
