jasonsbeer/Amiga-N2630/KiCAD/A2630-New-KiCAD-Rev410-PGA/Logic.kicad_sch

## KiCad design KiCAD/A2630-New-KiCAD-Rev410-PGA/Logic.kicad_sch (2024-03-27)

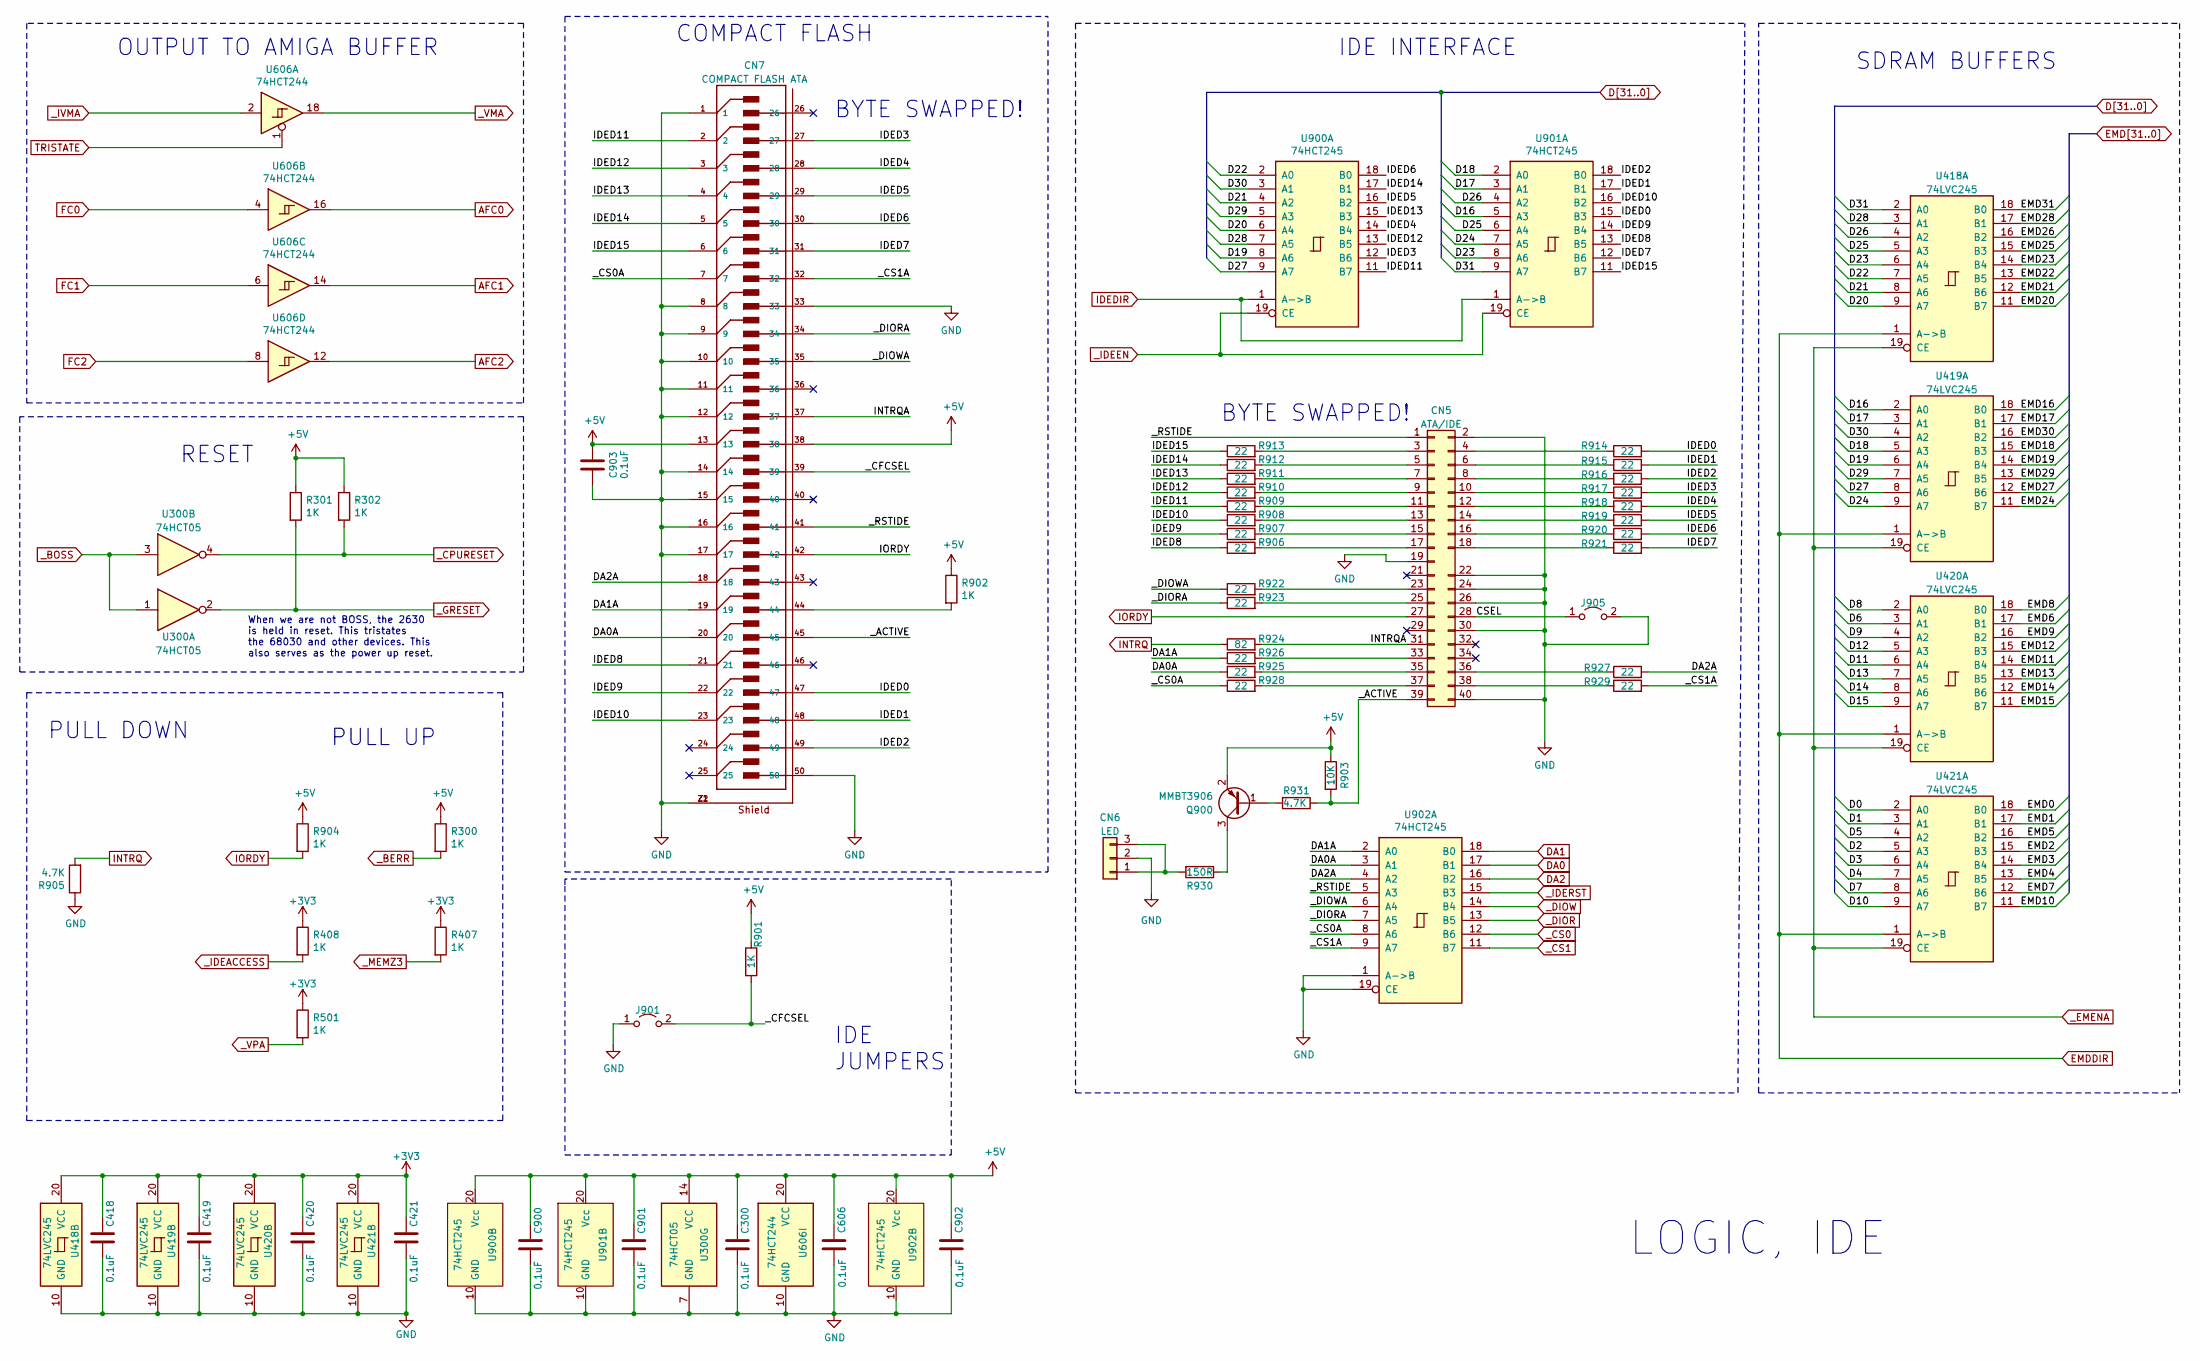
[picture p73: schematic Logic.kicad_sch]

Parts:
C300, C418, C419, C420, C421, C606, C900, C901, C902, C903: 0.1uF; C_0805_2012Metric
CN5: ATA/IDE; ATA_Header_2x20_P2.54mm
CN6: LED; PinHeader_1x03_P2.54mm_Vertical
CN7: COMPACT FLASH ATA; COMPACT-FLASH-SLOT; PART-NUMBER 693120035011
J901: CF SEL; PinHeader_1x02_P2.54mm_Vertical
J905: CABLE SELECT; PinHeader_1x02_P2.54mm_Vertical
Q900: MMBT3906; SOT-23
R300, R301, R302, R407, R408, R501, R901, R902, R904: 1K; R_0805_2012Metric
R903: 10K; R_0805_2012Metric
R905, R931: 4.7K; R_0805_2012Metric
R906, R907, R908, R909, R910, R911, R912, R913, R914, R915, R916, R917, R918, R919, R920, R921, R922, R923, R925, R926, R927, R928, R929: 22; R_0805_2012Metric
R924: 82; R_0805_2012Metric
R930: 150R; R_0805_2012Metric
U300: 74HCT05; SOIC-14_3.9x8.7mm_P1.27mm
U418, U419, U420, U421: 74LVC245; TSSOP-20_4.4x6.5mm_P0.65mm
U606: 74HCT244; SOIC-20W_7.5x12.8mm_P1.27mm
U900, U901, U902: 74HCT245; TSSOP-20_4.4x6.5mm_P0.65mm

Connections:
+3V3: C418.1, C419.1, C420.1, C421.1, R407.1, R408.1, R501.1, U418.20 (VCC), U419.20 (VCC), U420.20 (VCC), U421.20 (VCC)
+5V: C300.1, C606.1, C900.1, C901.1, C902.1, C903.1, CN7.13, CN7.38, Q900.2 (E), R300.1, R301.1, R302.1, R901.1, R902.1, R903.1, R904.1, U300.14 (VCC), U606.20 (VCC), U900.20 (Vcc), U901.20 (Vcc), U902.20 (Vcc)
AFC0: U606.16
AFC1: U606.14
AFC2: U606.12
CSEL: CN5.28, J905.1 (A)
D0: U421.2 (A0)
D1: U421.3 (A1)
D2: U421.5 (A3)
D3: U421.6 (A4)
D4: U421.7 (A5)
D5: U421.4 (A2)
D6: U420.3 (A1)
D7: U421.8 (A6)
D8: U420.2 (A0)
D9: U420.4 (A2)
D10: U421.9 (A7)
D11: U420.6 (A4)
D12: U420.5 (A3)
D13: U420.7 (A5)
D14: U420.8 (A6)
D15: U420.9 (A7)
D16: U419.2 (A0), U901.5 (A3)
D17: U419.3 (A1), U901.3 (A1)
D18: U419.5 (A3), U901.2 (A0)
D19: U419.6 (A4), U900.8 (A6)
D20: U418.9 (A7), U900.6 (A4)
D21: U418.8 (A6), U900.4 (A2)
D22: U418.7 (A5), U900.2 (A0)
D23: U418.6 (A4), U901.8 (A6)
D24: U419.9 (A7), U901.7 (A5)
D25: U418.5 (A3), U901.6 (A4)
D26: U418.4 (A2), U901.4 (A2)
D27: U419.8 (A6), U900.9 (A7)
D28: U418.3 (A1), U900.7 (A5)
D29: U419.7 (A5), U900.5 (A3)
D30: U419.4 (A2), U900.3 (A1)
D31: U418.2 (A0), U901.9 (A7)
DA0: U902.17 (B1)
DA0A: CN7.20, R925.1, U902.3 (A1)
DA1: U902.18 (B0)
DA1A: CN7.19, R926.1, U902.2 (A0)
DA2: U902.16 (B2)
DA2A: CN7.18, R927.2, U902.4 (A2)
EMD0: U421.18 (B0)
EMD1: U421.17 (B1)
EMD2: U421.15 (B3)
EMD3: U421.14 (B4)
EMD4: U421.13 (B5)
EMD5: U421.16 (B2)
EMD6: U420.17 (B1)
EMD7: U421.12 (B6)
EMD8: U420.18 (B0)
EMD9: U420.16 (B2)
EMD10: U421.11 (B7)
EMD11: U420.14 (B4)
EMD12: U420.15 (B3)
EMD13: U420.13 (B5)
EMD14: U420.12 (B6)
EMD15: U420.11 (B7)
EMD16: U419.18 (B0)
EMD17: U419.17 (B1)
EMD18: U419.15 (B3)
EMD19: U419.14 (B4)
EMD20: U418.11 (B7)
EMD21: U418.12 (B6)
EMD22: U418.13 (B5)
EMD23: U418.14 (B4)
EMD24: U419.11 (B7)
EMD25: U418.15 (B3)
EMD26: U418.16 (B2)
EMD27: U419.12 (B6)
EMD28: U418.17 (B1)
EMD29: U419.13 (B5)
EMD30: U419.16 (B2)
EMD31: U418.18 (B0)
EMDDIR: U418.1 (A->B), U419.1 (A->B), U420.1 (A->B), U421.1 (A->B)
FC0: U606.4
FC1: U606.6
FC2: U606.8
GND: C300.2, C418.2, C419.2, C420.2, C421.2, C606.2, C900.2, C901.2, C902.2, C903.2, CN5.2, CN5.19, CN5.22, CN5.24, CN5.26, CN5.30, CN5.40, CN6.2, CN7.1, CN7.8, CN7.9, CN7.10, CN7.11, CN7.12, CN7.14, CN7.15, CN7.16, CN7.17, CN7.33, CN7.50, CN7.Z1, CN7.Z2, J901.1 (A), J905.2 (B), R905.1, U300.7 (GND), U418.10 (GND), U419.10 (GND), U420.10 (GND), U421.10 (GND), U606.10 (GND), U900.10 (GND), U901.10 (GND), U902.1 (A->B), U902.10 (GND), U902.19 (CE)
IDED0: CN7.47, R914.2, U901.15 (B3)
IDED1: CN7.48, R915.2, U901.17 (B1)
IDED2: CN7.49, R916.2, U901.18 (B0)
IDED3: CN7.27, R917.2, U900.12 (B6)
IDED4: CN7.28, R918.2, U900.14 (B4)
IDED5: CN7.29, R919.2, U900.16 (B2)
IDED6: CN7.30, R920.2, U900.18 (B0)
IDED7: CN7.31, R921.2, U901.12 (B6)
IDED8: CN7.21, R906.1, U901.13 (B5)
IDED9: CN7.22, R907.1, U901.14 (B4)
IDED10: CN7.23, R908.1, U901.16 (B2)
IDED11: CN7.2, R909.1, U900.11 (B7)
IDED12: CN7.3, R910.1, U900.13 (B5)
IDED13: CN7.4, R911.1, U900.15 (B3)
IDED14: CN7.5, R912.1, U900.17 (B1)
IDED15: CN7.6, R913.1, U901.11 (B7)
IDEDIR: U900.1 (A->B), U901.1 (A->B)
INTRQ: R905.2, R924.1
INTRQA: CN5.31, CN7.37, R924.2
IORDY: CN5.27, CN7.42, R904.2
unnamed: CN5.3, R913.2
unnamed: CN5.4, R914.1
unnamed: CN5.5, R912.2
unnamed: CN5.6, R915.1
unnamed: CN5.7, R911.2
unnamed: CN5.8, R916.1
unnamed: CN5.9, R910.2
unnamed: CN5.10, R917.1
unnamed: CN5.11, R909.2
unnamed: CN5.12, R918.1
unnamed: CN5.13, R908.2
unnamed: CN5.14, R919.1
unnamed: CN5.15, R907.2
unnamed: CN5.16, R920.1
unnamed: CN5.17, R906.2
unnamed: CN5.18, R921.1
unnamed: CN5.23, R922.2
unnamed: CN5.25, R923.2
unnamed: CN5.33, R926.2
unnamed: CN5.35, R925.2
unnamed: CN5.36, R927.1
unnamed: CN5.37, R928.2
unnamed: CN5.38, R929.1
unnamed: CN6.1, CN6.3, R930.2
unnamed: CN7.44, R902.2
unnamed: Q900.1 (B), R931.2
unnamed: Q900.3 (C), R930.1
TRISTATE: U606.1
_ACTIVE: CN5.39, CN7.45, R903.2, R931.1
_BERR: R300.2
_BOSS: U300.1, U300.3
_CFCSEL: CN7.39, J901.2 (B), R901.2
_CPURESET: R302.2, U300.4
_CS0: U902.12 (B6)
_CS0A: CN7.7, R928.1, U902.8 (A6)
_CS1: U902.11 (B7)
_CS1A: CN7.32, R929.2, U902.9 (A7)
_DIOR: U902.13 (B5)
_DIORA: CN7.34, R923.1, U902.7 (A5)
_DIOW: U902.14 (B4)
_DIOWA: CN7.35, R922.1, U902.6 (A4)
_EMENA: U418.19 (CE), U419.19 (CE), U420.19 (CE), U421.19 (CE)
_GRESET: R301.2, U300.2
_IDEACCESS: R408.2
_IDEEN: U900.19 (CE), U901.19 (CE)
_IDERST: U902.15 (B3)
_IVMA: U606.2
_MEMZ3: R407.2
_RSTIDE: CN5.1, CN7.41, U902.5 (A3)
_VMA: U606.18
_VPA: R501.2

Notes on the sheet:
PULL DOWN
IDE INTERFACE
BYTE SWAPPED!
PULL UP
RESET
IDE JUMPERS
LOGIC, IDE
When we are not BOSS, the 2630 is held in reset. This tristates the 68030 and other devices. This also serves as the power up reset.
OUTPUT TO AMIGA BUFFER
SDRAM BUFFERS
COMPACT FLASH
