jasonsbeer/Amiga-N2630/KiCAD/A2630-New-KiCAD-Rev410-PGA/Processor.kicad_sch

## KiCad design KiCAD/A2630-New-KiCAD-Rev410-PGA/Processor.kicad_sch (2024-03-27)

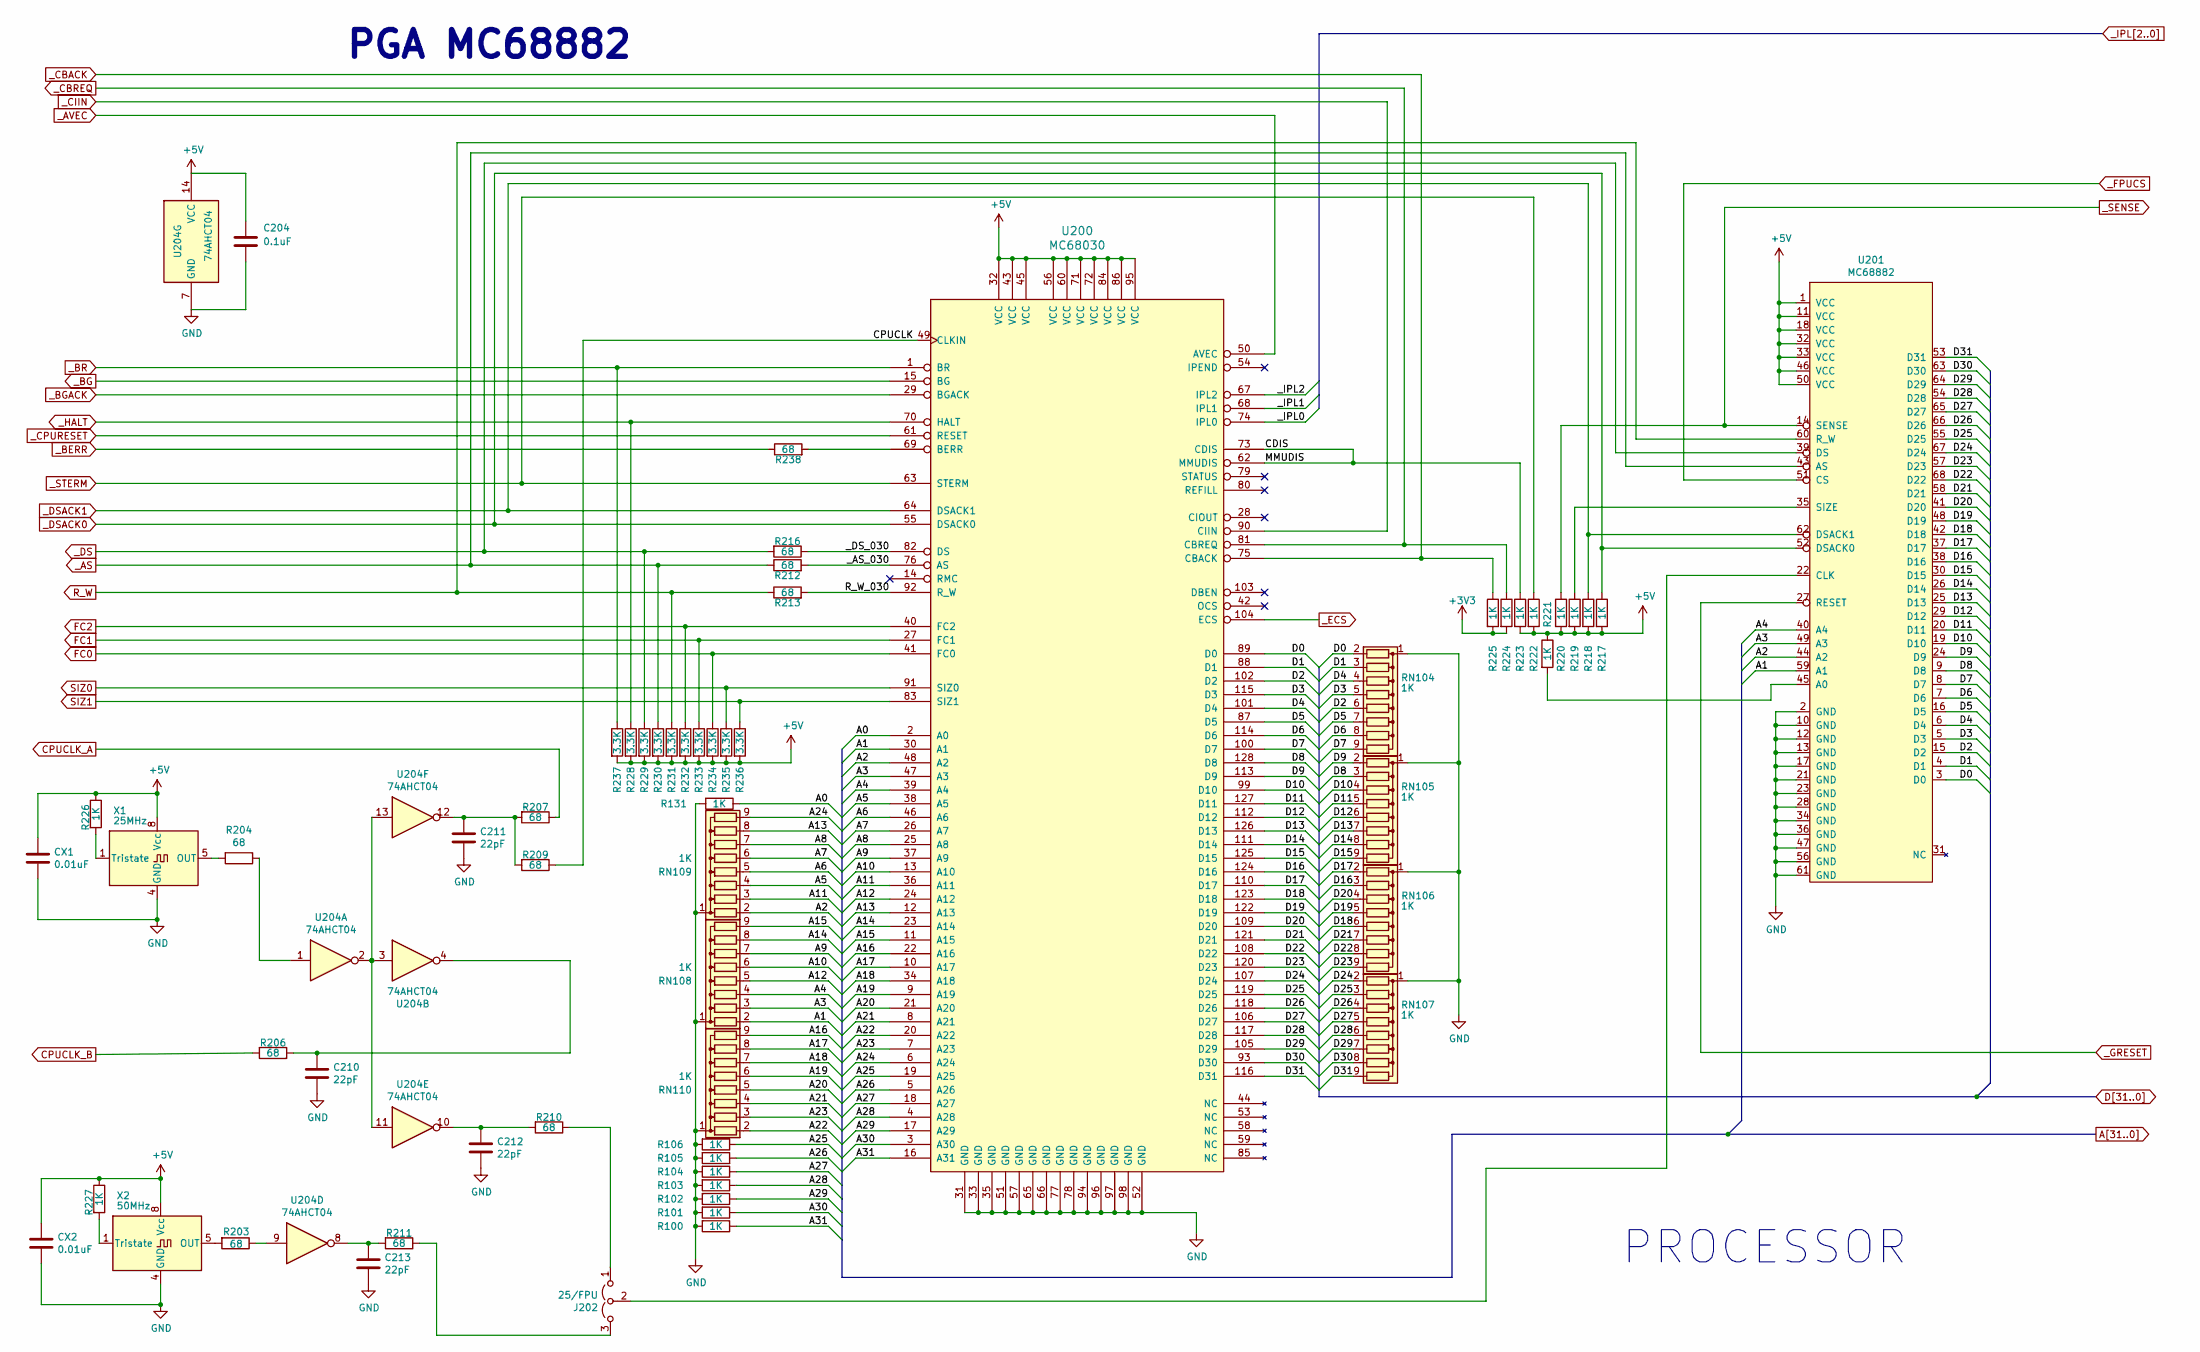
[picture p74: schematic Processor.kicad_sch]

Parts:
C204: 0.1uF; C_0805_2012Metric
C210, C211, C212, C213: 22pF; C_0805_2012Metric
CX1, CX2: 0.01uF; C_0805_2012Metric
J202: 25/FPU; PinHeader_1x03_P2.54mm_Vertical
R100, R101, R102, R103, R104, R105, R106, R131, R217, R218, R219, R220, R221, R222, R223, R224, R225, R226, R227: 1K; R_0805_2012Metric
R203, R204, R206, R207, R209, R210, R211, R212, R213, R216, R238: 68; R_0805_2012Metric
R228, R229, R230, R231, R232, R233, R234, R235, R236, R237: 3.3K; R_0805_2012Metric
RN104, RN105, RN106, RN107, RN108, RN109, RN110: 1K; R_Array_SIP9
U200: MC68030; MC68030-PGA
U201: MC68882; MC68882-PGA
U204: 74AHCT04; SOIC-14_3.9x8.7mm_P1.27mm; Digikey 296-31832-1-ND
X1: 25MHz; Oscillator_DIP-8; Digikey 535-9175-5-ND
X2: 50MHz; Oscillator_DIP-8; Digikey 535-9175-5-ND

Connections:
+3V3: R224.2, R225.2
+5V: C204.1, CX1.1, CX2.1, R217.2, R218.2, R219.2, R220.2, R221.1, R222.2, R223.2, R226.1, R227.1, R228.2, R229.2, R230.2, R231.2, R232.2, R233.2, R234.2, R235.2, R236.2, R237.2, U200.32 (VCC), U200.43 (VCC), U200.45 (VCC), U200.56 (VCC), U200.60 (VCC), U200.71 (VCC), U200.72 (VCC), U200.84 (VCC), U200.86 (VCC), U200.95 (VCC), U201.1 (VCC), U201.11 (VCC), U201.18 (VCC), U201.32 (VCC), U201.33 (VCC), U201.46 (VCC), U201.50 (VCC), U204.14 (VCC), X1.8 (Vcc), X2.8 (Vcc)
A0: R131.1, U200.2 (A0)
A1: RN108.2 (R1), U200.30 (A1), U201.59 (A1)
A2: RN109.2 (R1), U200.48 (A2), U201.44 (A2)
A3: RN108.3 (R2), U200.47 (A3), U201.49 (A3)
A4: RN108.4 (R3), U200.39 (A4), U201.40 (A4)
A5: RN109.4 (R3), U200.38 (A5)
A6: RN109.5 (R4), U200.46 (A6)
A7: RN109.6 (R5), U200.26 (A7)
A8: RN109.7 (R6), U200.25 (A8)
A9: RN108.7 (R6), U200.37 (A9)
A10: RN108.6 (R5), U200.13 (A10)
A11: RN109.3 (R2), U200.36 (A11)
A12: RN108.5 (R4), U200.24 (A12)
A13: RN109.8 (R7), U200.12 (A13)
A14: RN108.8 (R7), U200.23 (A14)
A15: RN108.9 (R8), U200.11 (A15)
A16: RN110.9 (R8), U200.22 (A16)
A17: RN110.8 (R7), U200.10 (A17)
A18: RN110.7 (R6), U200.34 (A18)
A19: RN110.6 (R5), U200.9 (A19)
A20: RN110.5 (R4), U200.21 (A20)
A21: RN110.4 (R3), U200.8 (A21)
A22: RN110.2 (R1), U200.20 (A22)
A23: RN110.3 (R2), U200.7 (A23)
A24: RN109.9 (R8), U200.6 (A24)
A25: R106.1, U200.19 (A25)
A26: R105.1, U200.5 (A26)
A27: R104.1, U200.18 (A27)
A28: R103.1, U200.4 (A28)
A29: R102.1, U200.17 (A29)
A30: R101.1, U200.3 (A30)
A31: R100.1, U200.16 (A31)
CDIS: R223.1, U200.62 (MMUDIS), U200.73 (CDIS)
CPUCLK: R209.1, U200.49 (CLKIN)
CPUCLK_A: R207.1
CPUCLK_B: R206.2
D0: RN104.2 (R1), U200.89 (D0), U201.3 (D0)
D1: RN104.3 (R2), U200.88 (D1), U201.4 (D1)
D2: RN104.6 (R5), U200.102 (D2), U201.15 (D2)
D3: RN104.5 (R4), U200.115 (D3), U201.5 (D3)
D4: RN104.4 (R3), U200.101 (D4), U201.6 (D4)
D5: RN104.7 (R6), U200.87 (D5), U201.16 (D5)
D6: RN104.8 (R7), U200.114 (D6), U201.7 (D6)
D7: RN104.9 (R8), U200.100 (D7), U201.8 (D7)
D8: RN105.3 (R2), U200.128 (D8), U201.9 (D8)
D9: RN105.2 (R1), U200.113 (D9), U201.24 (D9)
D10: RN105.4 (R3), U200.99 (D10), U201.19 (D10)
D11: RN105.5 (R4), U200.127 (D11), U201.20 (D11)
D12: RN105.6 (R5), U200.112 (D12), U201.29 (D12)
D13: RN105.7 (R6), U200.126 (D13), U201.25 (D13)
D14: RN105.8 (R7), U200.111 (D14), U201.26 (D14)
D15: RN105.9 (R8), U200.125 (D15), U201.30 (D15)
D16: RN106.3 (R2), U200.124 (D16), U201.38 (D16)
D17: RN106.2 (R1), U200.110 (D17), U201.37 (D17)
D18: RN106.6 (R5), U200.123 (D18), U201.42 (D18)
D19: RN106.5 (R4), U200.122 (D19), U201.48 (D19)
D20: RN106.4 (R3), U200.109 (D20), U201.41 (D20)
D21: RN106.7 (R6), U200.121 (D21), U201.58 (D21)
D22: RN106.8 (R7), U200.108 (D22), U201.68 (D22)
D23: RN106.9 (R8), U200.120 (D23), U201.57 (D23)
D24: RN107.2 (R1), U200.107 (D24), U201.67 (D24)
D25: RN107.3 (R2), U200.119 (D25), U201.55 (D25)
D26: RN107.4 (R3), U200.118 (D26), U201.66 (D26)
D27: RN107.5 (R4), U200.106 (D27), U201.65 (D27)
D28: RN107.6 (R5), U200.117 (D28), U201.54 (D28)
D29: RN107.7 (R6), U200.105 (D29), U201.64 (D29)
D30: RN107.8 (R7), U200.93 (D30), U201.63 (D30)
D31: RN107.9 (R8), U200.116 (D31), U201.53 (D31)
FC0: R234.1, U200.41 (FC0)
FC1: R233.1, U200.27 (FC1)
FC2: R232.1, U200.40 (FC2)
GND: C204.2, C210.2, C211.2, C212.2, C213.2, CX1.2, CX2.2, R100.2, R101.2, R102.2, R103.2, R104.2, R105.2, R106.2, R131.2, RN104.1 (common), RN105.1 (common), RN106.1 (common), RN107.1 (common), RN108.1 (common), RN109.1 (common), RN110.1 (common), U200.31 (GND), U200.33 (GND), U200.35 (GND), U200.51 (GND), U200.52 (GND), U200.57 (GND), U200.65 (GND), U200.66 (GND), U200.77 (GND), U200.78 (GND), U200.94 (GND), U200.96 (GND), U200.97 (GND), U200.98 (GND), U201.2 (GND), U201.10 (GND), U201.12 (GND), U201.13 (GND), U201.17 (GND), U201.21 (GND), U201.23 (GND), U201.28 (GND), U201.34 (GND), U201.36 (GND), U201.47 (GND), U201.56 (GND), U201.61 (GND), U204.7 (GND), X1.4 (GND), X2.4 (GND)
unnamed: C210.1, R206.1, U204.4
unnamed: C211.1, R207.2, R209.2, U204.12
unnamed: C212.1, R210.2, U204.10
unnamed: C213.1, R211.2, U204.8
unnamed: J202.1 (A), R210.1
unnamed: J202.2 (C), U201.22 (CLK)
unnamed: J202.3 (B), R211.1
unnamed: R203.1, U204.9
unnamed: R203.2, X2.5 (OUT)
unnamed: R204.1, U204.1
unnamed: R204.2, X1.5 (OUT)
unnamed: R219.1, U201.35 (SIZE)
unnamed: R221.2, U201.45 (A0)
unnamed: R226.2, X1.1 (Tristate)
unnamed: R227.2, X2.1 (Tristate)
unnamed: R238.2, U200.69 (BERR)
unnamed: U204.2, U204.3, U204.11, U204.13
R_W: R213.1, R231.1, U201.60 (R_W)
R_W_030: R213.2, U200.92 (R_W)
SIZ0: R235.1, U200.91 (SIZ0)
SIZ1: R236.1, U200.83 (SIZ1)
_AS: R212.1, R230.1, U201.43 (AS)
_AS_030: R212.2, U200.76 (AS)
_AVEC: U200.50 (AVEC)
_BERR: R238.1
_BG: U200.15 (BG)
_BGACK: U200.29 (BGACK)
_BR: R237.1, U200.1 (BR)
_CBACK: R225.1, U200.75 (CBACK)
_CBREQ: R224.1, U200.81 (CBREQ)
_CIIN: U200.90 (CIIN)
_CPURESET: U200.61 (RESET)
_DS: R216.2, R229.1, U201.39 (DS)
_DSACK0: R217.1, U200.55 (DSACK0), U201.52 (DSACK0)
_DSACK1: R218.1, U200.64 (DSACK1), U201.62 (DSACK1)
_DS_030: R216.1, U200.82 (DS)
_ECS: U200.104 (ECS)
_FPUCS: U201.51 (CS)
_GRESET: U201.27 (RESET)
_HALT: R228.1, U200.70 (HALT)
_IPL0: U200.74 (IPL0)
_IPL1: U200.68 (IPL1)
_IPL2: U200.67 (IPL2)
_SENSE: R220.1, U201.14 (SENSE)
_STERM: R222.1, U200.63 (STERM)

Notes on the sheet:
PROCESSOR
PGA MC68882
